misterblack1/zenith_zt1/pictures/Zenith ZT-1 Under capacitor.jpg

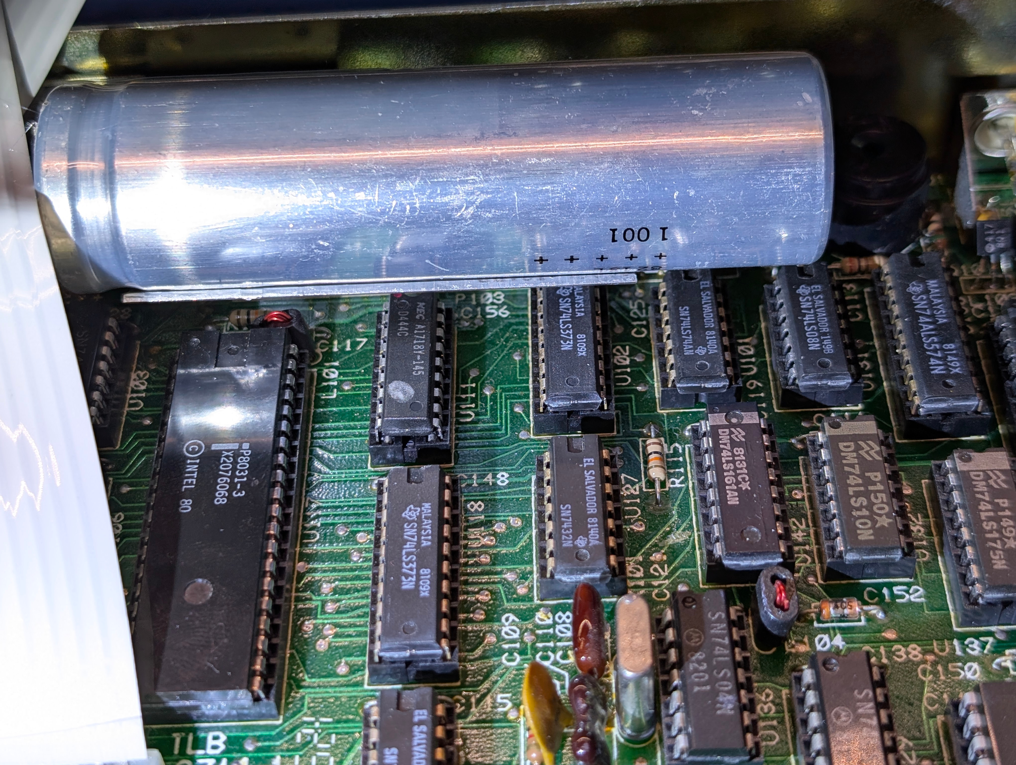
pictures/Zenith ZT-1 Under capacitor.jpg
