misterblack1/zenith_zt1/pictures/zenith_zt11/01 Zenith ZT-11.jpg

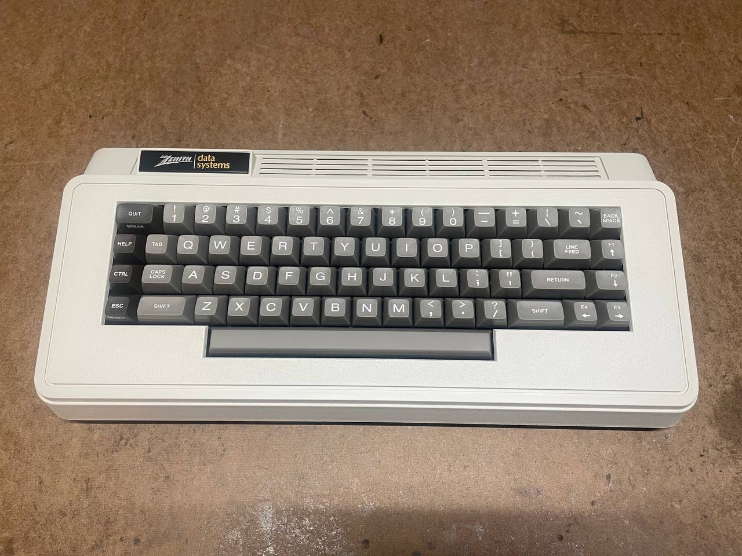
pictures/zenith_zt11/01 Zenith ZT-11.jpg
