misterblack1/zenith_zt1/pictures/zenith_zt11/02 Zenith ZT-11 Underside.jpg

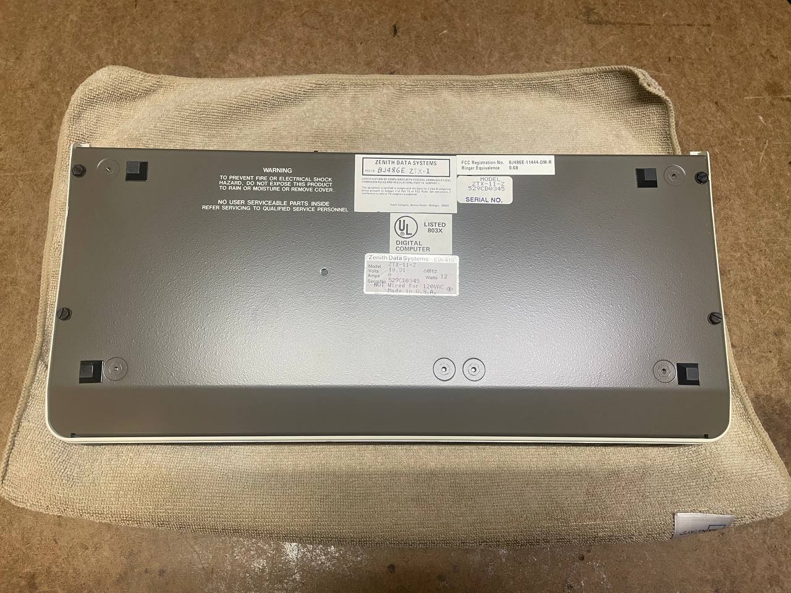
pictures/zenith_zt11/02 Zenith ZT-11 Underside.jpg
