misterblack1/zenith_zt1/pictures/zenith_zt11/03 Zenith ZT-11 Labels.jpg

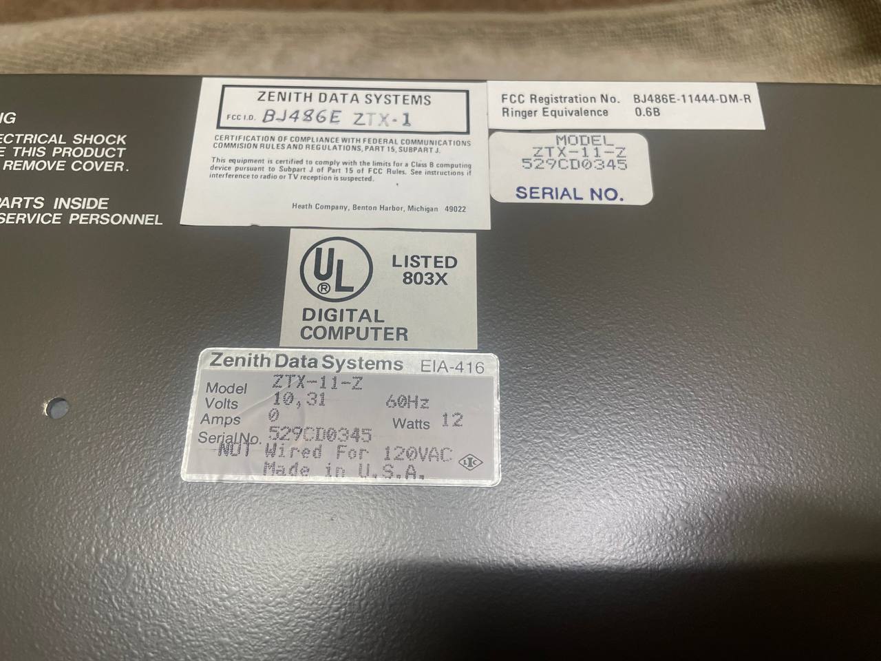
pictures/zenith_zt11/03 Zenith ZT-11 Labels.jpg
