misterblack1/zenith_zt1/pictures/zenith_zt11/04 Zenith ZT-11 Keyboard connection.jpg

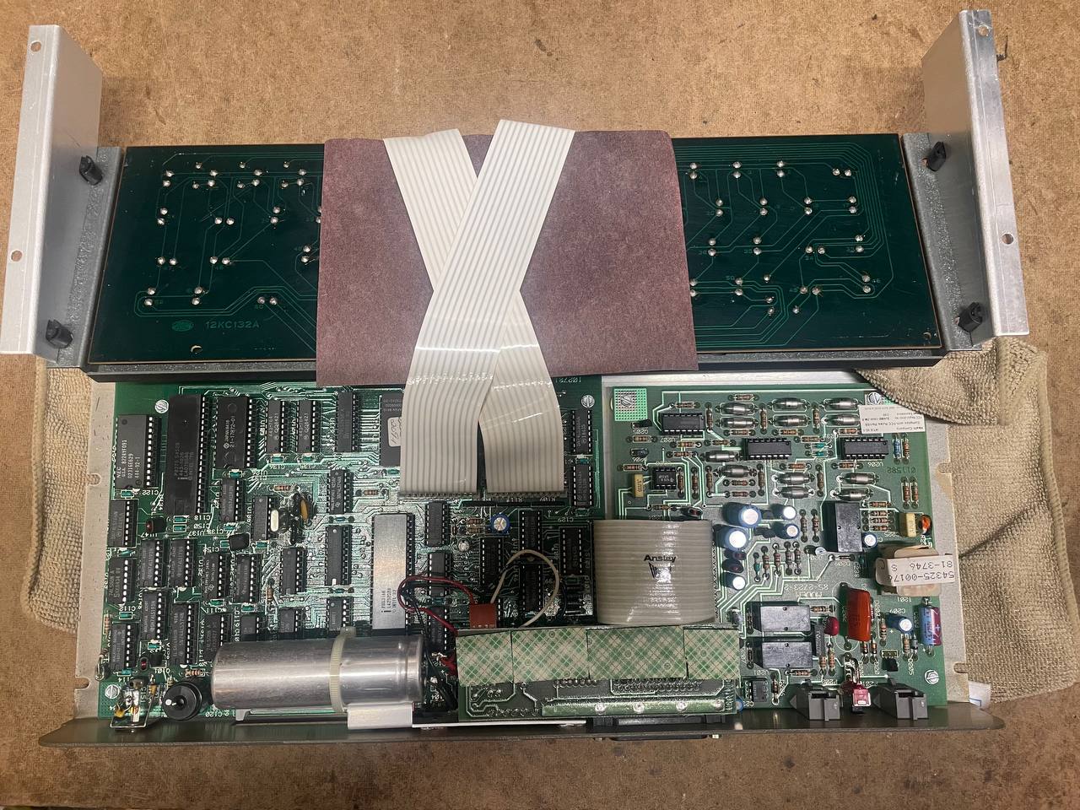
pictures/zenith_zt11/04 Zenith ZT-11 Keyboard connection.jpg
