misterblack1/zenith_zt1/pictures/zenith_zt11/05 Zenith ZT-11 Keyboard connection close up.jpg

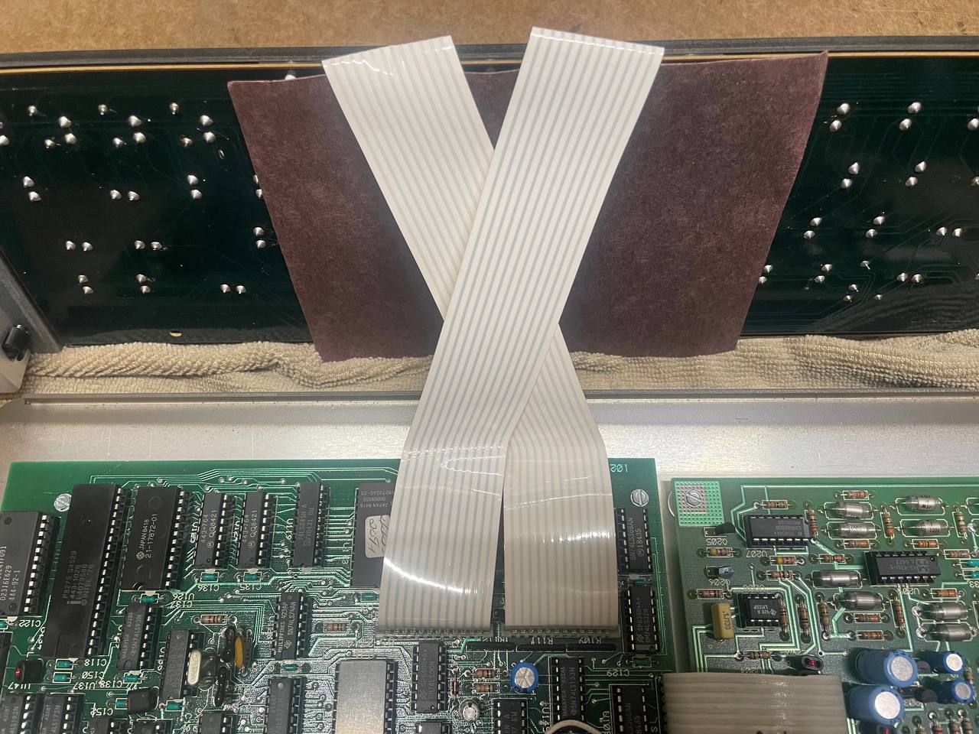
pictures/zenith_zt11/05 Zenith ZT-11 Keyboard connection close up.jpg
