misterblack1/zenith_zt1/pictures/zenith_zt11/06  Zenith ZT-11 Internals.jpg

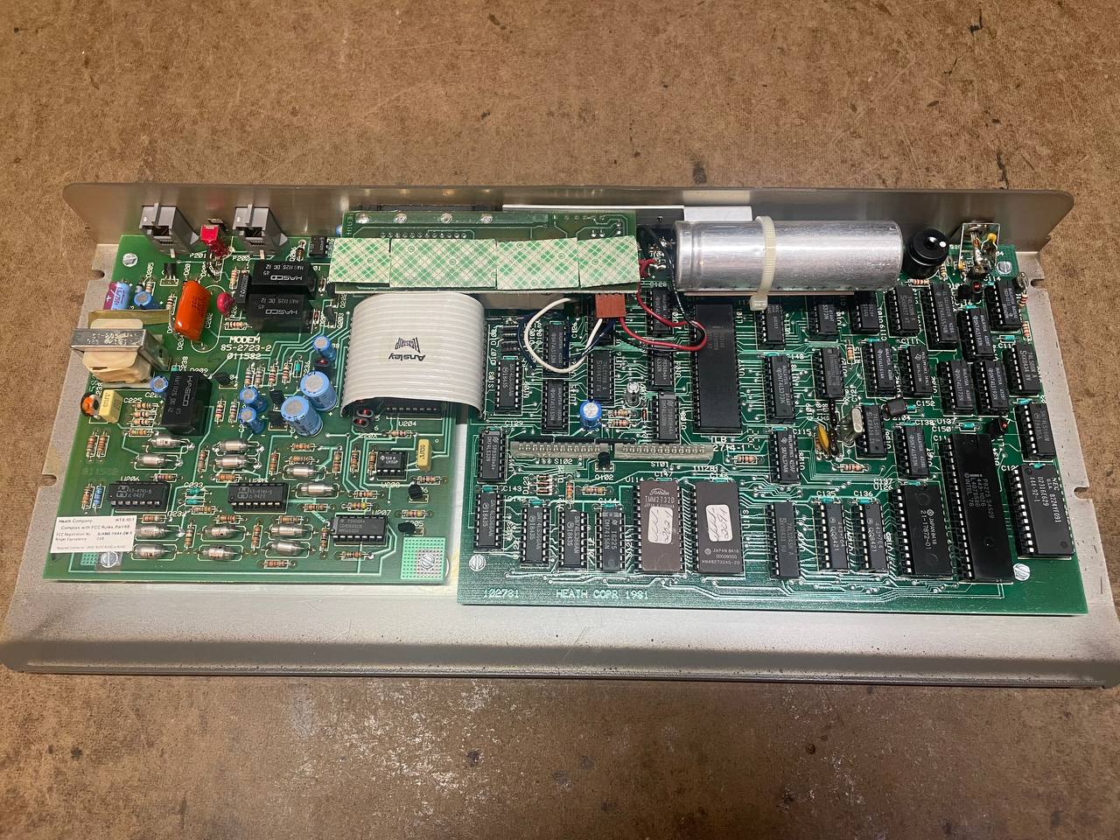
pictures/zenith_zt11/06 Zenith ZT-11 Internals.jpg
