misterblack1/zenith_zt1/pictures/zenith_zt11/08 Zenith ZT-11 Serial Add-on Board.jpg

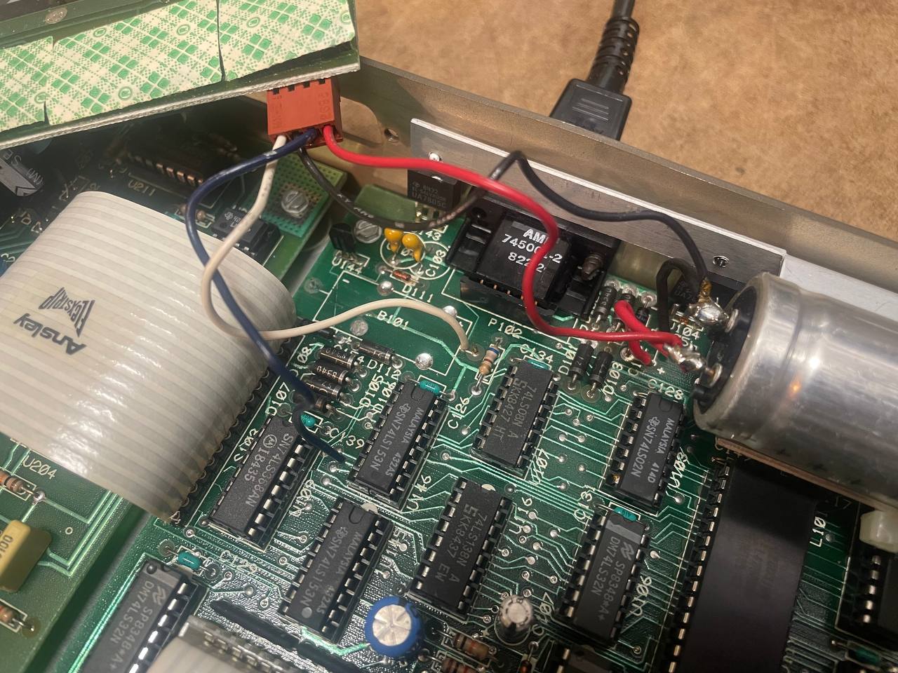
pictures/zenith_zt11/08 Zenith ZT-11 Serial Add-on Board.jpg
