misterblack1/zenith_zt1/pictures/zenith_zt11/11 Zenith ZT-11 Power on screen.jpg

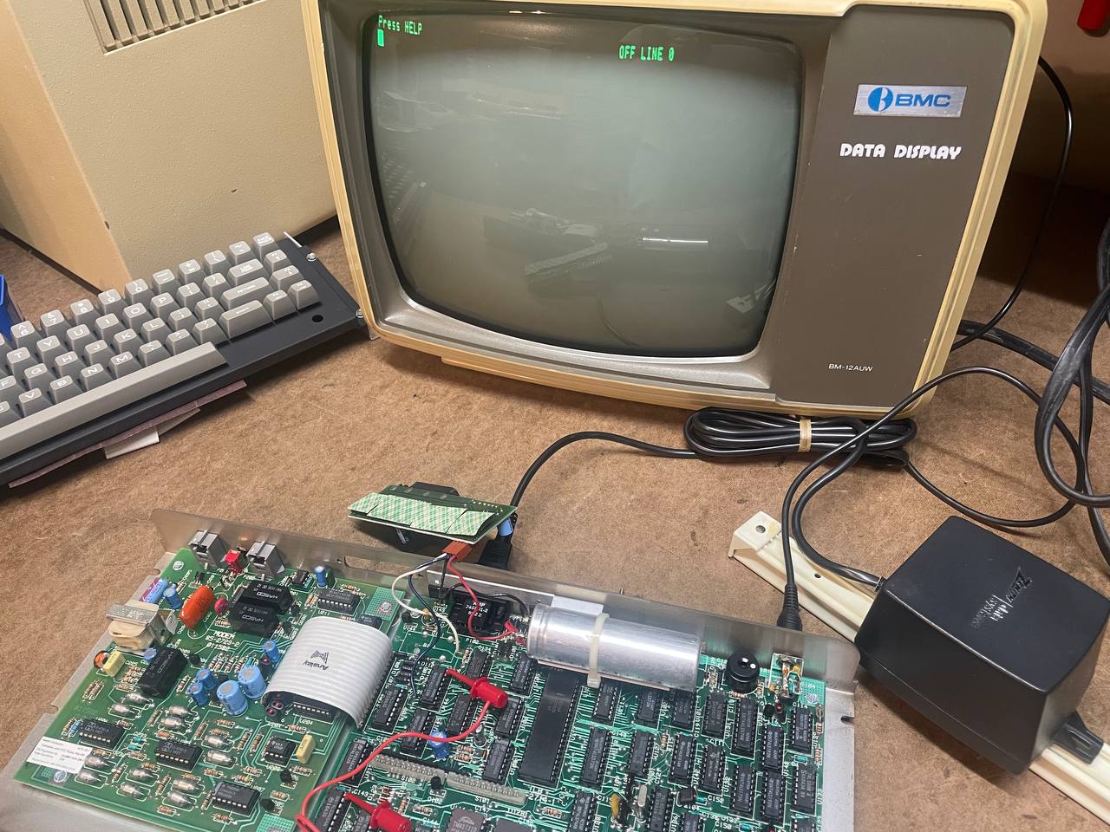
pictures/zenith_zt11/11 Zenith ZT-11 Power on screen.jpg
