misterblack1/zenith_zt1/pictures/zenith_zt11/13 Zenith ZT-11 Setup.jpg

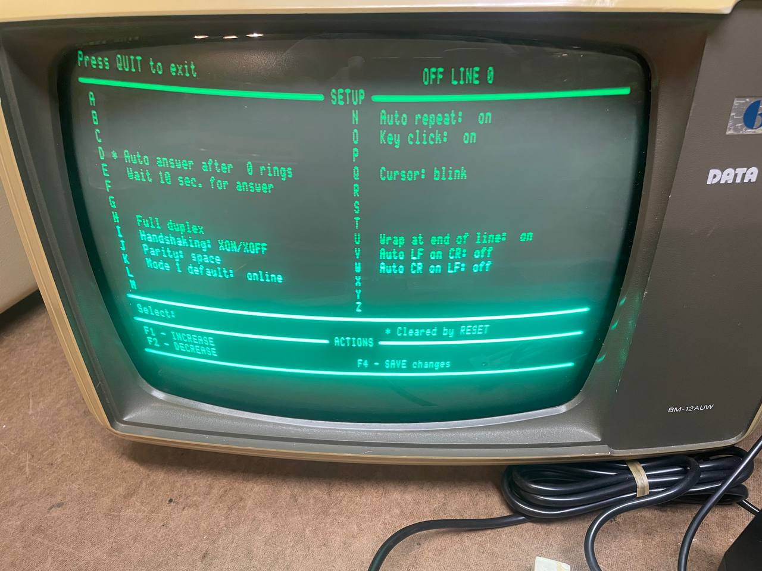
pictures/zenith_zt11/13 Zenith ZT-11 Setup.jpg
