misterblack1/zenith_zt1/ZT1 Schematics/DMA.kicad_sch

## KiCad design ZT1 Schematics/DMA.kicad_sch (2025-08-11)

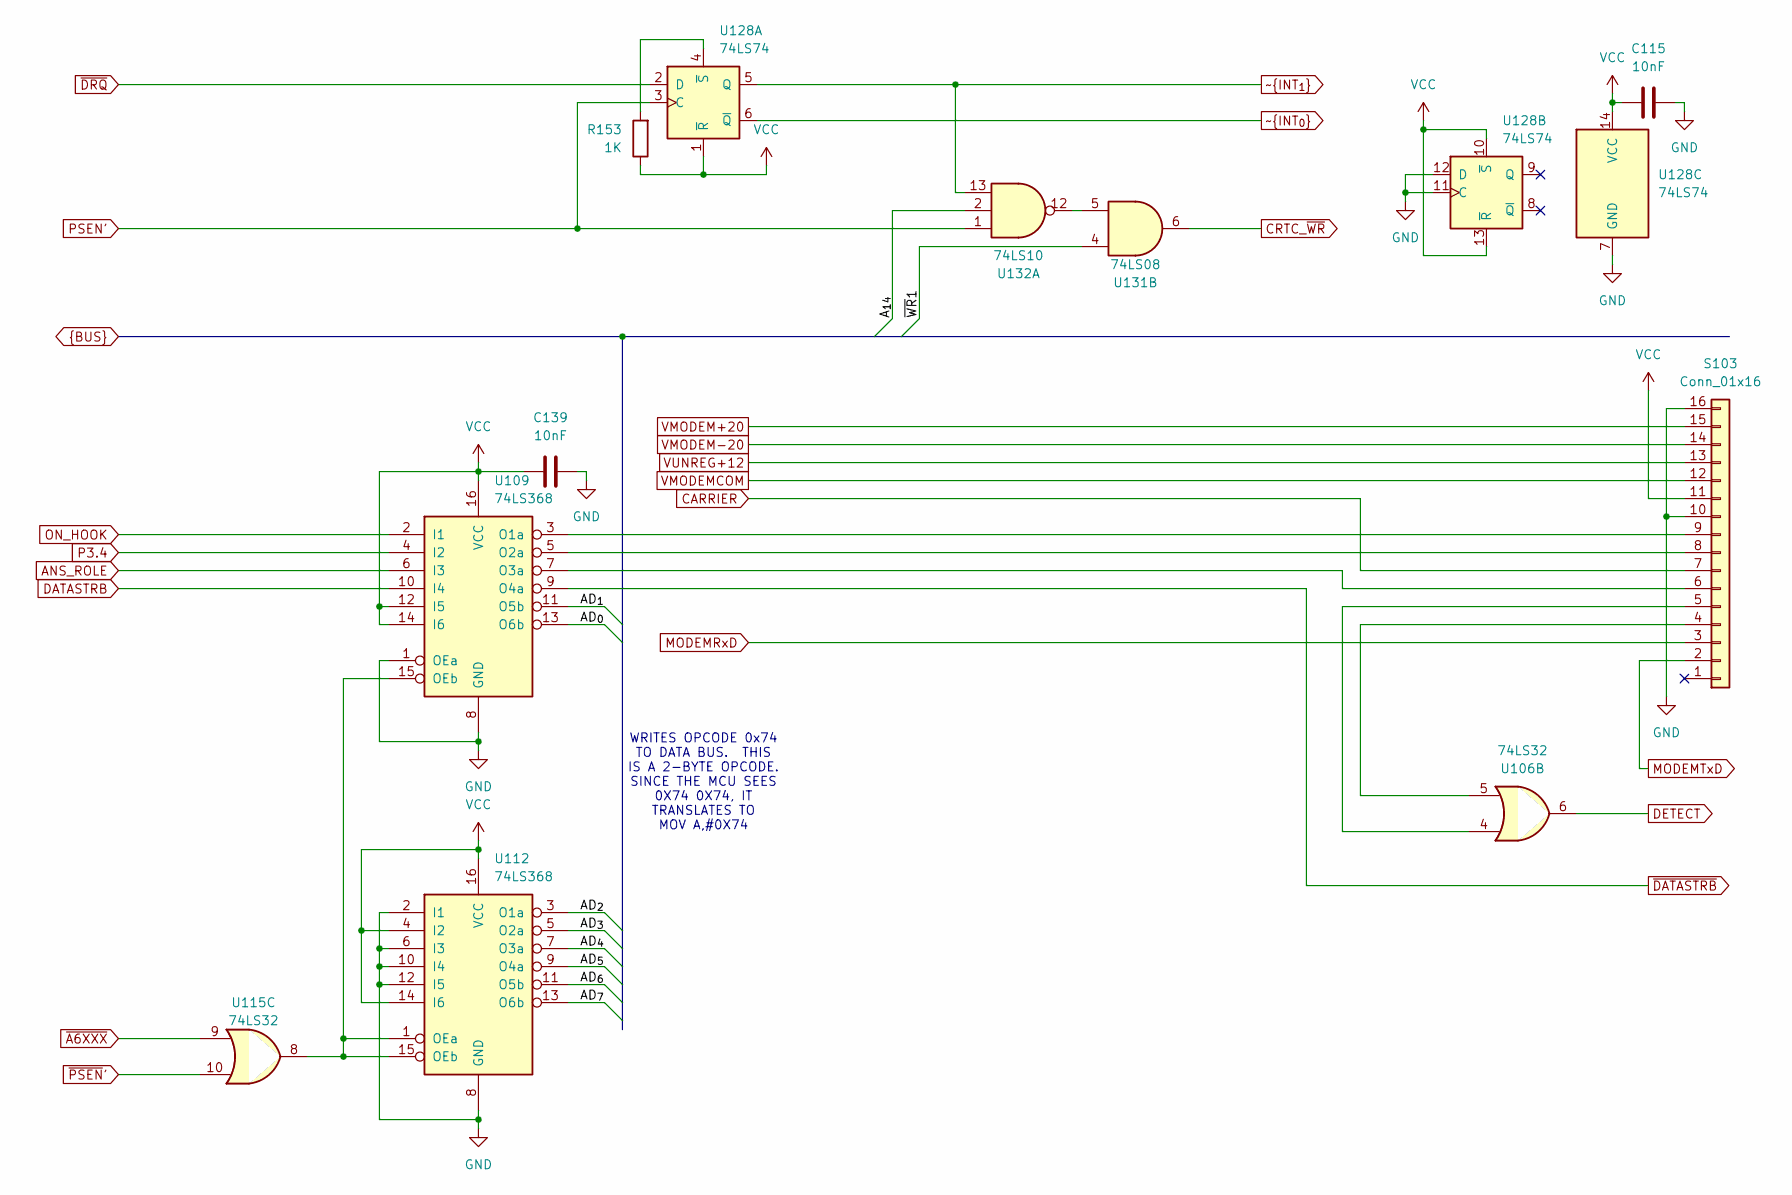
[picture p27: schematic DMA.kicad_sch]

Parts:
C115, C139: 10nF; C_350mil
R153: 1K; R_450mil
S103: Conn_01x16; PinHeader_1x16_P2.54mm_Vertical
U106, U115: 74LS32; DIP-14_W7.62mm
U109, U112: 74LS368; DIP-16_W7.62mm
U128: 74LS74; DIP-14_W7.62mm
U131: 74LS08; DIP-14_W7.62mm
U132: 74LS10; DIP-14_W7.62mm

Connections:
AD_{0}: U109.13 (O6b)
AD_{1}: U109.11 (O5b)
AD_{2}: U112.3 (O1a)
AD_{3}: U112.5 (O2a)
AD_{4}: U112.7 (O3a)
AD_{5}: U112.9 (O4a)
AD_{6}: U112.11 (O5b)
AD_{7}: U112.13 (O6b)
ANS_ROLE: U109.6 (I3)
A_{14}: U132.2
CARRIER: S103.7
CRTC_~WR: U131.6
DATASTRB: U109.10 (I4)
DETECT: U106.6
GND: C115.2, C139.2, S103.10, S103.16, U109.1 (OEa), U109.8 (GND), U112.2 (I1), U112.6 (I3), U112.8 (GND), U112.10 (I4), U112.12 (I5), U128.7 (GND), U128.11 (C), U128.12 (D)
MODEMRxD: S103.3
MODEMTxD: S103.2
unnamed: R153.2, U128.4 (~S)
unnamed: S103.4, U106.5
unnamed: S103.5, U106.4
unnamed: S103.6, U109.7 (O3a)
unnamed: S103.8, U109.5 (O2a)
unnamed: S103.9, U109.3 (O1a)
unnamed: U109.15 (OEb), U112.1 (OEa), U112.15 (OEb), U115.8
unnamed: U131.5, U132.12
ON_HOOK: U109.2 (I1)
P3.4: U109.4 (I2)
PSEN': U128.3 (C), U132.1
VCC: C115.1, C139.1, R153.1, S103.11, U109.12 (I5), U109.14 (I6), U109.16 (VCC), U112.4 (I2), U112.14 (I6), U112.16 (VCC), U128.1 (~R), U128.10 (~S), U128.13 (~R), U128.14 (VCC)
VMODEM+20: S103.15
VMODEM-20: S103.14
VMODEMCOM: S103.12
VUNREG+12: S103.13
~A6XXX: U115.9
~DATASTRB: U109.9 (O4a)
~DRQ: U128.2 (D)
~INT_{0}: U128.6 (~Q)
~INT_{1}: U128.5 (Q), U132.13
~PSEN': U115.10
~WR1: U131.4

Notes on the sheet:
WRITES OPCODE 0x74 TO DATA BUS. THIS IS A 2-BYTE OPCODE. SINCE THE MCU SEES 0X74 0X74, IT TRANSLATES TO MOV A,#0X74
