misterblack1/zenith_zt1/ZT1 Schematics/MCU.kicad_sch

## KiCad design ZT1 Schematics/MCU.kicad_sch (2025-08-11)

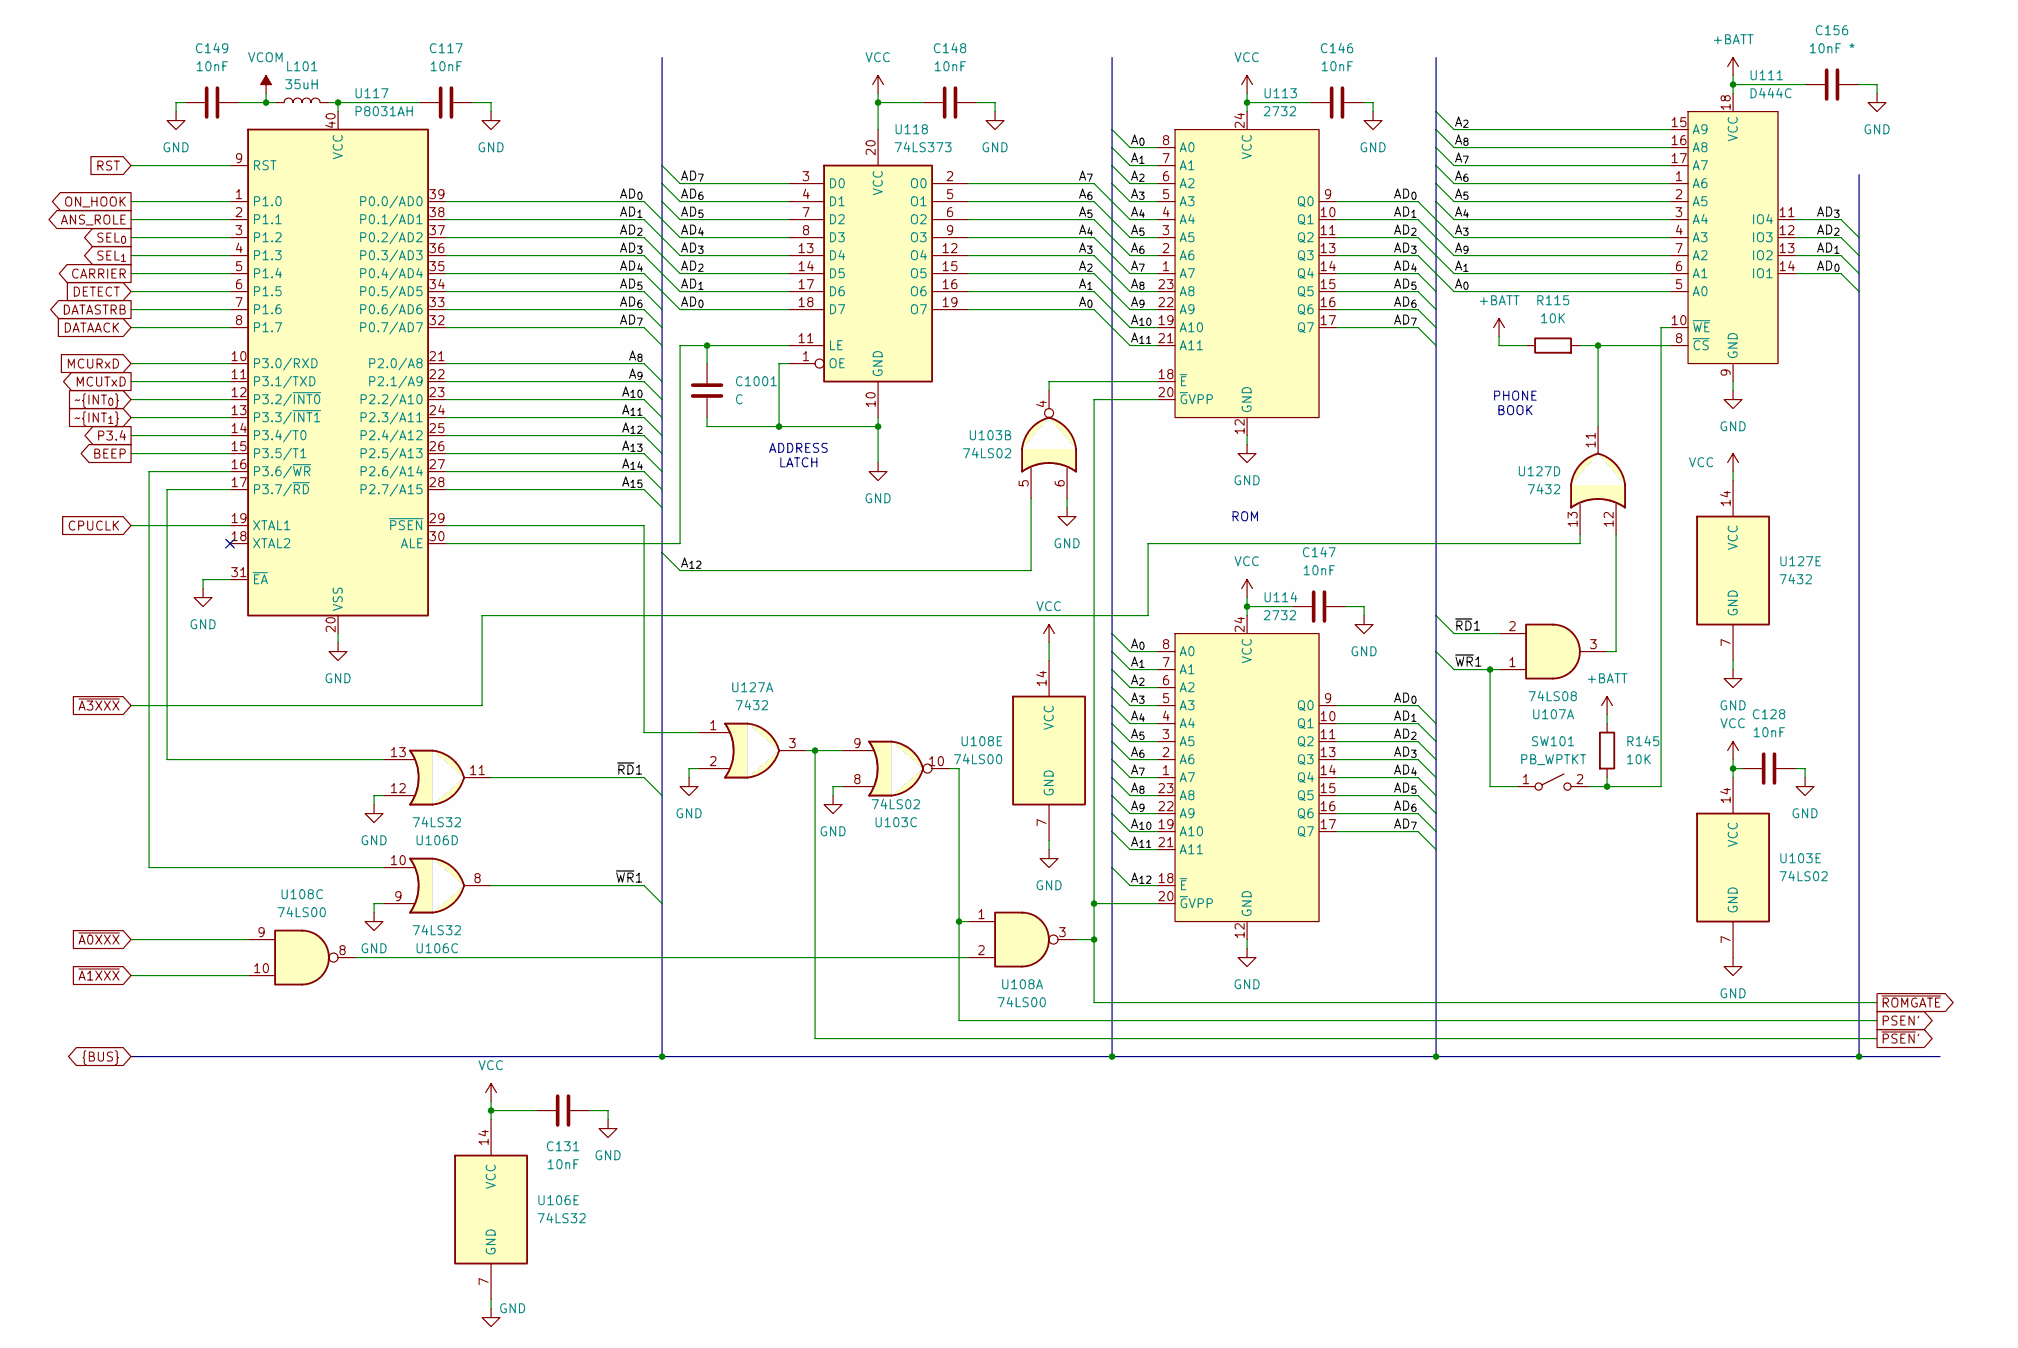
[picture p28: schematic MCU.kicad_sch]

Parts:
C117, C128, C131, C146, C147, C148, C149: 10nF; C_350mil
C156: 10nF *; C_350mil
C1001: C; C_Disc_P7.62
L101: 35uH; L_Axial_L7.0mm_D3.3mm_P5.08mm_Vertical_Fastron_MICC
R115, R145: 10K; R_450mil
SW101: PB_WPTKT; SW_DIP_SPSTx01_Slide_6.7x4.1mm_W7.62mm_P2.54mm_LowProfile
U103: 74LS02; DIP-14_W7.62mm
U106: 74LS32; DIP-14_W7.62mm
U107: 74LS08; DIP-14_W7.62mm
U108: 74LS00; DIP-14_W7.62mm
U111: D444C; DIP-18_W7.62mm
U113, U114: 2732; DIP-24_W15.24mm
U117: P8031AH; DIP-40_W15.24mm
U118: 74LS373; DIP-20_W7.62mm
U127: 7432; DIP-14_W7.62mm

Connections:
+BATT: C156.1, R115.1, R145.1, U111.18 (VCC)
AD_{0}: U111.14 (IO1), U113.9 (Q0), U114.9 (Q0), U117.39 (P0.0/AD0), U118.18 (D7)
AD_{1}: U111.13 (IO2), U113.10 (Q1), U114.10 (Q1), U117.38 (P0.1/AD1), U118.17 (D6)
AD_{2}: U111.12 (IO3), U113.11 (Q2), U114.11 (Q2), U117.37 (P0.2/AD2), U118.14 (D5)
AD_{3}: U111.11 (IO4), U113.13 (Q3), U114.13 (Q3), U117.36 (P0.3/AD3), U118.13 (D4)
AD_{4}: U113.14 (Q4), U114.14 (Q4), U117.35 (P0.4/AD4), U118.8 (D3)
AD_{5}: U113.15 (Q5), U114.15 (Q5), U117.34 (P0.5/AD5), U118.7 (D2)
AD_{6}: U113.16 (Q6), U114.16 (Q6), U117.33 (P0.6/AD6), U118.4 (D1)
AD_{7}: U113.17 (Q7), U114.17 (Q7), U117.32 (P0.7/AD7), U118.3 (D0)
ANS_ROLE: U117.2 (P1.1)
A_{0}: U111.5 (A0), U113.8 (A0), U114.8 (A0), U118.19 (O7)
A_{1}: U111.6 (A1), U113.7 (A1), U114.7 (A1), U118.16 (O6)
A_{2}: U111.15 (A9), U113.6 (A2), U114.6 (A2), U118.15 (O5)
A_{3}: U111.4 (A3), U113.5 (A3), U114.5 (A3), U118.12 (O4)
A_{4}: U111.3 (A4), U113.4 (A4), U114.4 (A4), U118.9 (O3)
A_{5}: U111.2 (A5), U113.3 (A5), U114.3 (A5), U118.6 (O2)
A_{6}: U111.1 (A6), U113.2 (A6), U114.2 (A6), U118.5 (O1)
A_{7}: U111.17 (A7), U113.1 (A7), U114.1 (A7), U118.2 (O0)
A_{8}: U111.16 (A8), U113.23 (A8), U114.23 (A8), U117.21 (P2.0/A8)
A_{9}: U111.7 (A2), U113.22 (A9), U114.22 (A9), U117.22 (P2.1/A9)
A_{10}: U113.19 (A10), U114.19 (A10), U117.23 (P2.2/A10)
A_{11}: U113.21 (A11), U114.21 (A11), U117.24 (P2.3/A11)
A_{12}: U103.5, U114.18 (~E), U117.25 (P2.4/A12)
A_{13}: U117.26 (P2.5/A13)
A_{14}: U117.27 (P2.6/A14)
A_{15}: U117.28 (P2.7/A15)
BEEP: U117.15 (P3.5/T1)
CARRIER: U117.5 (P1.4)
CPUCLK: U117.19 (XTAL1)
DATAACK: U117.8 (P1.7)
DATASTRB: U117.7 (P1.6)
DETECT: U117.6 (P1.5)
GND: C117.2, C128.2, C131.2, C146.2, C147.2, C148.2, C149.1, C156.2, C1001.2, U103.6, U103.7 (GND), U103.8, U106.7 (GND), U106.9, U106.12, U108.7 (GND), U111.9 (GND), U113.12 (GND), U114.12 (GND), U117.20 (VSS), U117.31 (~EA), U118.1 (OE), U118.10 (GND), U127.2, U127.7 (GND)
MCURxD: U117.10 (P3.0/RXD)
MCUTxD: U117.11 (P3.1/TXD)
unnamed: C117.1, L101.2, U117.40 (VCC)
unnamed: C1001.1, U117.30 (ALE), U118.11 (LE)
unnamed: R115.2, U111.8 (~CS), U127.11
unnamed: R145.2, SW101.2 (B), U111.10 (~WE)
unnamed: U103.4, U113.18 (~E)
unnamed: U106.10, U117.16 (P3.6/~WR)
unnamed: U106.13, U117.17 (P3.7/~RD)
unnamed: U107.3, U127.12
unnamed: U108.2, U108.8
unnamed: U117.29 (~PSEN), U127.1
ON_HOOK: U117.1 (P1.0)
P3.4: U117.14 (P3.4/T0)
PSEN': U103.10, U108.1
RST: U117.9 (RST)
SEL_{0}: U117.3 (P1.2)
SEL_{1}: U117.4 (P1.3)
VCC: C128.1, C131.1, C146.1, C147.1, C148.1, U103.14 (VCC), U106.14 (VCC), U108.14 (VCC), U113.24 (VCC), U114.24 (VCC), U118.20 (VCC), U127.14 (VCC)
VCOM: C149.2, L101.1
~A0XXX: U108.9
~A1XXX: U108.10
~A3XXX: U127.13
~INT_{0}: U117.12 (P3.2/~INT0)
~INT_{1}: U117.13 (P3.3/~INT1)
~PSEN': U103.9, U127.3
~RD1: U106.11, U107.2
~ROMGATE: U108.3, U113.20 (~GVPP), U114.20 (~GVPP)
~WR1: SW101.1 (A), U106.8, U107.1

Notes on the sheet:
PHONE BOOK
ROM
ADDRESS LATCH
