misterblack1/zenith_zt1/ZT1 Schematics/Oscillator.kicad_sch

## KiCad design ZT1 Schematics/Oscillator.kicad_sch (2025-08-11)

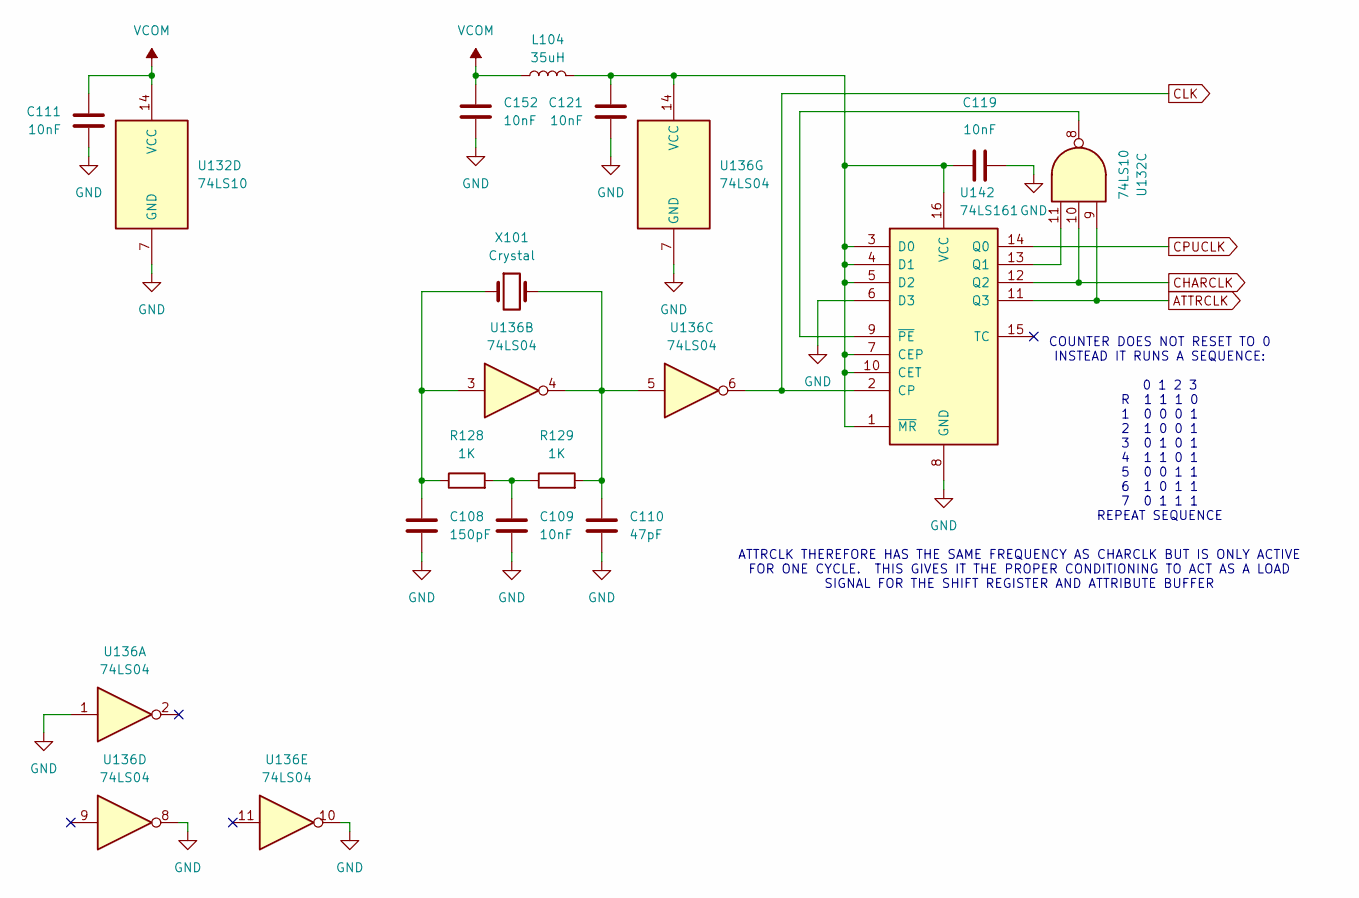
[picture p29: schematic Oscillator.kicad_sch]

Parts:
C108: 150pF; C_Disc_D9.0mm_W2.5mm_P7.50mm
C109: 10nF; C_Disc_D9.0mm_W2.5mm_P7.50mm
C110: 47pF; C_Disc_D9.0mm_W2.5mm_P7.50mm
C111, C119, C121, C152: 10nF; C_350mil
L104: 35uH; L_Axial_L7.0mm_D3.3mm_P5.08mm_Vertical_Fastron_MICC
R128, R129: 1K; R_450mil
U132: 74LS10; DIP-14_W7.62mm
U136: 74LS04; DIP-14_W7.62mm
U142: 74LS161; DIP-16_W7.62mm
X101: Crystal; Crystal_HC18-U_Vertical

Connections:
ATTRCLK: U132.9, U142.11 (Q3)
CHARCLK: U132.10, U142.12 (Q2)
CLK: U136.6, U142.2 (CP)
CPUCLK: U142.14 (Q0)
GND: C108.2, C109.2, C110.2, C111.2, C119.2, C121.2, C152.2, U132.7 (GND), U136.1, U136.7 (GND), U136.8, U136.10, U142.6 (D3), U142.8 (GND)
unnamed: C108.1, R128.1, U136.3, X101.1
unnamed: C109.1, R128.2, R129.1
unnamed: C110.1, R129.2, U136.4, U136.5, X101.2
unnamed: C119.1, C121.1, L104.2, U136.14 (VCC), U142.1 (~MR), U142.3 (D0), U142.4 (D1), U142.5 (D2), U142.7 (CEP), U142.10 (CET), U142.16 (VCC)
unnamed: U132.8, U142.9 (~PE)
unnamed: U132.11, U142.13 (Q1)
VCOM: C111.1, C152.1, L104.1, U132.14 (VCC)

Notes on the sheet:
ATTRCLK THEREFORE HAS THE SAME FREQUENCY AS CHARCLK BUT IS ONLY ACTIVE FOR ONE CYCLE. THIS GIVES IT THE PROPER CONDITIONING TO ACT AS A LOAD SIGNAL FOR THE SHIFT REGISTER AND ATTRIBUTE BUFFER
COUNTER DOES NOT RESET TO 0 INSTEAD IT RUNS A SEQUENCE: 0 1 2 3 R 1 1 1 0 1 0 0 0 1 2 1 0 0 1 3 0 1 0 1 4 1 1 0 1 5 0 0 1 1 6 1 0 1 1 7 0 1 1 1 REPEAT SEQUENCE
