misterblack1/zenith_zt1/ZT1 Schematics/VRAM.kicad_sch

## KiCad design ZT1 Schematics/VRAM.kicad_sch (2025-08-11)

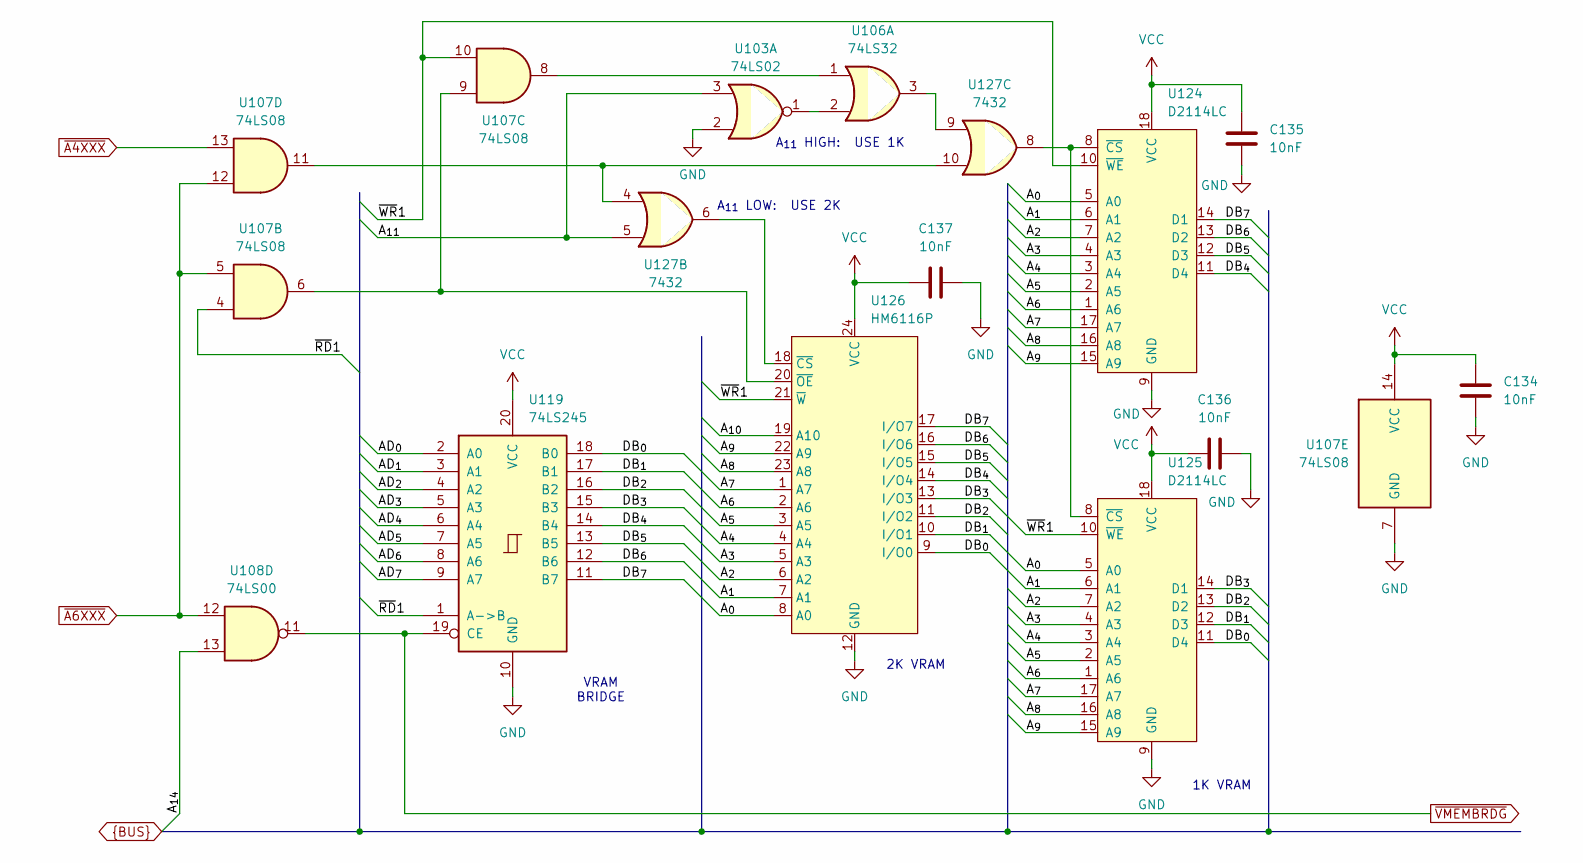
[picture p30: schematic VRAM.kicad_sch]

Parts:
C134, C135, C136, C137: 10nF; C_350mil
U103: 74LS02; DIP-14_W7.62mm
U106: 74LS32; DIP-14_W7.62mm
U107: 74LS08; DIP-14_W7.62mm
U108: 74LS00; DIP-14_W7.62mm
U119: 74LS245; DIP-20_W7.62mm
U124, U125: D2114LC; DIP-18_W7.62mm
U126: HM6116P; DIP-24_W15.24mm
U127: 7432; DIP-14_W7.62mm

Connections:
AD_{0}: U119.2 (A0)
AD_{1}: U119.3 (A1)
AD_{2}: U119.4 (A2)
AD_{3}: U119.5 (A3)
AD_{4}: U119.6 (A4)
AD_{5}: U119.7 (A5)
AD_{6}: U119.8 (A6)
AD_{7}: U119.9 (A7)
A_{0}: U124.5 (A0), U125.5 (A0), U126.8 (A0)
A_{1}: U124.6 (A1), U125.6 (A1), U126.7 (A1)
A_{2}: U124.7 (A2), U125.7 (A2), U126.6 (A2)
A_{3}: U124.4 (A3), U125.4 (A3), U126.5 (A3)
A_{4}: U124.3 (A4), U125.3 (A4), U126.4 (A4)
A_{5}: U124.2 (A5), U125.2 (A5), U126.3 (A5)
A_{6}: U124.1 (A6), U125.1 (A6), U126.2 (A6)
A_{7}: U124.17 (A7), U125.17 (A7), U126.1 (A7)
A_{8}: U124.16 (A8), U125.16 (A8), U126.23 (A8)
A_{9}: U124.15 (A9), U125.15 (A9), U126.22 (A9)
A_{10}: U126.19 (A10)
A_{11}: U103.3, U127.5
A_{14}: U108.13
DB_{0}: U119.18 (B0), U125.11 (D4), U126.9 (I/O0)
DB_{1}: U119.17 (B1), U125.12 (D3), U126.10 (I/O1)
DB_{2}: U119.16 (B2), U125.13 (D2), U126.11 (I/O2)
DB_{3}: U119.15 (B3), U125.14 (D1), U126.13 (I/O3)
DB_{4}: U119.14 (B4), U124.11 (D4), U126.14 (I/O4)
DB_{5}: U119.13 (B5), U124.12 (D3), U126.15 (I/O5)
DB_{6}: U119.12 (B6), U124.13 (D2), U126.16 (I/O6)
DB_{7}: U119.11 (B7), U124.14 (D1), U126.17 (I/O7)
GND: C134.2, C135.2, C136.2, C137.2, U103.2, U107.7 (GND), U119.10 (GND), U124.9 (GND), U125.9 (GND), U126.12 (GND)
unnamed: U103.1, U106.2
unnamed: U106.1, U107.8
unnamed: U106.3, U127.9
unnamed: U107.6, U107.9, U126.20 (~OE)
unnamed: U107.11, U127.4, U127.10
unnamed: U124.8 (~CS), U125.8 (~CS), U127.8
unnamed: U126.18 (~CS), U127.6
VCC: C134.1, C135.1, C136.1, C137.1, U107.14 (VCC), U119.20 (VCC), U124.18 (VCC), U125.18 (VCC), U126.24 (VCC)
~A4XXX: U107.13
~A6XXX: U107.5, U107.12, U108.12
~RD1: U107.4, U119.1 (A->B)
~VMEMBRDG: U108.11, U119.19 (CE)
~WR1: U107.10, U124.10 (~WE), U125.10 (~WE), U126.21 (~W)

Notes on the sheet:
2K VRAM
VRAM BRIDGE
A_{11} HIGH: USE 1K
1K VRAM
A_{11} LOW: USE 2K
