misterblack1/zenith_zt1/ZT1 Schematics/ZX1.kicad_sch

## KiCad design ZT1 Schematics/ZX1.kicad_sch (2025-08-11)

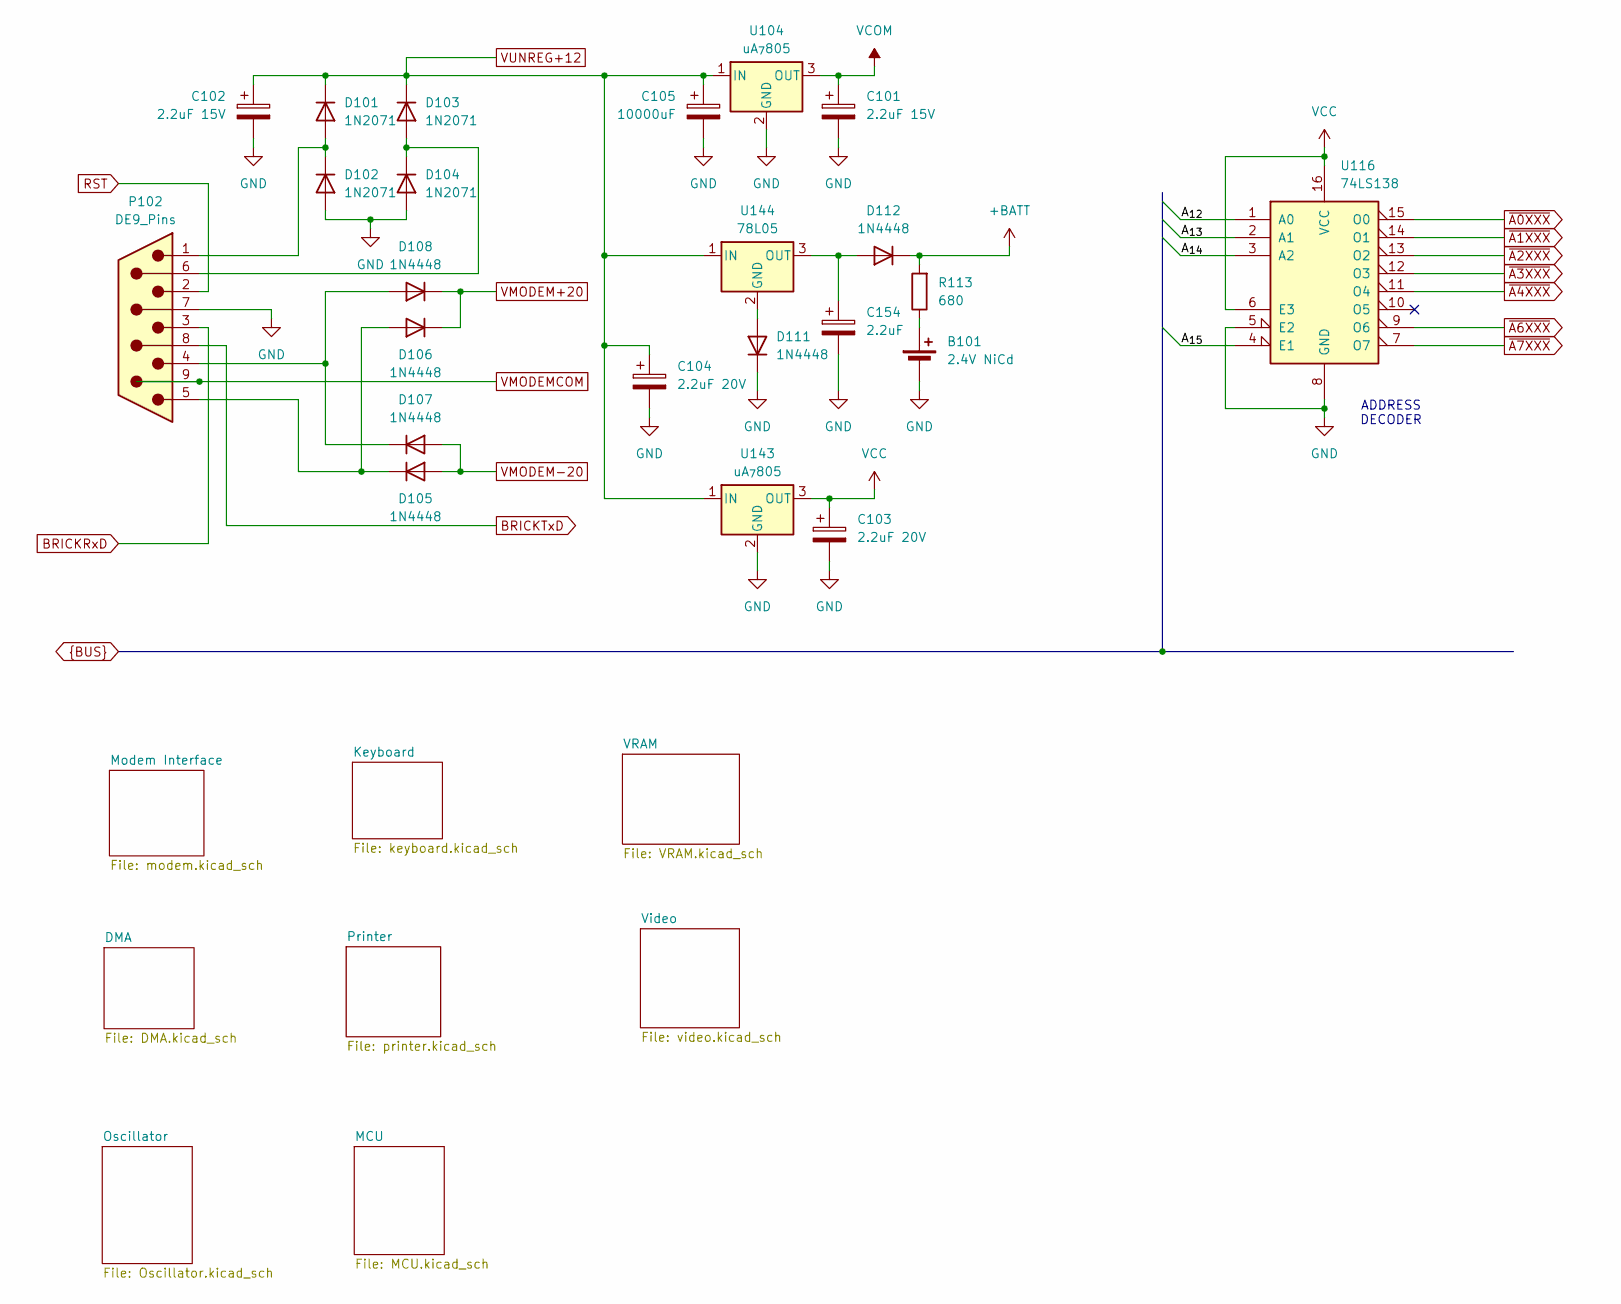
[picture p31: schematic ZX1.kicad_sch]

Parts:
B101: 2.4V NiCd; Battery
C101, C102: 2.2uF 15V; CP_520mil
C103, C104: 2.2uF 20V; CP_Radial_D8.0mm_P5.00mm
C105: 10000uF; CP_Radial_D10.0mm_P5.00mm
C154: 2.2uF; CP_350mil
D101, D102, D103, D104: 1N2071; D_DO-34_SOD68_P10.16mm_Horizontal
D105, D106, D107, D108, D111, D112: 1N4448; D_350mil
P102: DE9_Pins; DSUB-9_Pins_Horizontal_P2.77x2.54mm_EdgePinOffset9.40mm
R113: 680; R_450mil
U104, U143: uA_{7}805; TO-220-3_Vertical
U116: 74LS138; DIP-16_W7.62mm
U144: 78L05; TO-220-3_Vertical

Connections:
+BATT: D112.1 (K), R113.2
A_{12}: U116.1 (A0)
A_{13}: U116.2 (A1)
A_{14}: U116.3 (A2)
A_{15}: U116.4 (E1)
BRICKRxD: P102.3
BRICKTxD: P102.8
GND: B101.2 (-), C101.2, C102.2, C103.2, C104.2, C105.2, C154.2, D102.2 (A), D104.2 (A), D111.1 (K), P102.7, U104.2 (GND), U116.5 (E2), U116.8 (GND), U143.2 (GND)
unnamed: B101.1 (+), R113.1
unnamed: C154.1, D112.2 (A), U144.3 (OUT)
unnamed: D101.2 (A), D102.1 (K), P102.1
unnamed: D103.2 (A), D104.1 (K), P102.6
unnamed: D105.1 (K), D106.2 (A), P102.5
unnamed: D107.1 (K), D108.2 (A), P102.4
unnamed: D111.2 (A), U144.2 (GND)
RST: P102.2
VCC: C103.1, U116.6 (E3), U116.16 (VCC), U143.3 (OUT)
VCOM: C101.1, U104.3 (OUT)
VMODEM+20: D106.1 (K), D108.1 (K)
VMODEM-20: D105.2 (A), D107.2 (A)
VMODEMCOM: P102.9
VUNREG+12: C102.1, C104.1, C105.1, D101.1 (K), D103.1 (K), U104.1 (IN), U143.1 (IN), U144.1 (IN)
~A0XXX: U116.15 (O0)
~A1XXX: U116.14 (O1)
~A2XXX: U116.13 (O2)
~A3XXX: U116.12 (O3)
~A4XXX: U116.11 (O4)
~A6XXX: U116.9 (O6)
~A7XXX: U116.7 (O7)

Notes on the sheet:
ADDRESS DECODER
