misterblack1/zenith_zt1/ZT1 Schematics/keyboard.kicad_sch

## KiCad design ZT1 Schematics/keyboard.kicad_sch (2025-08-11)

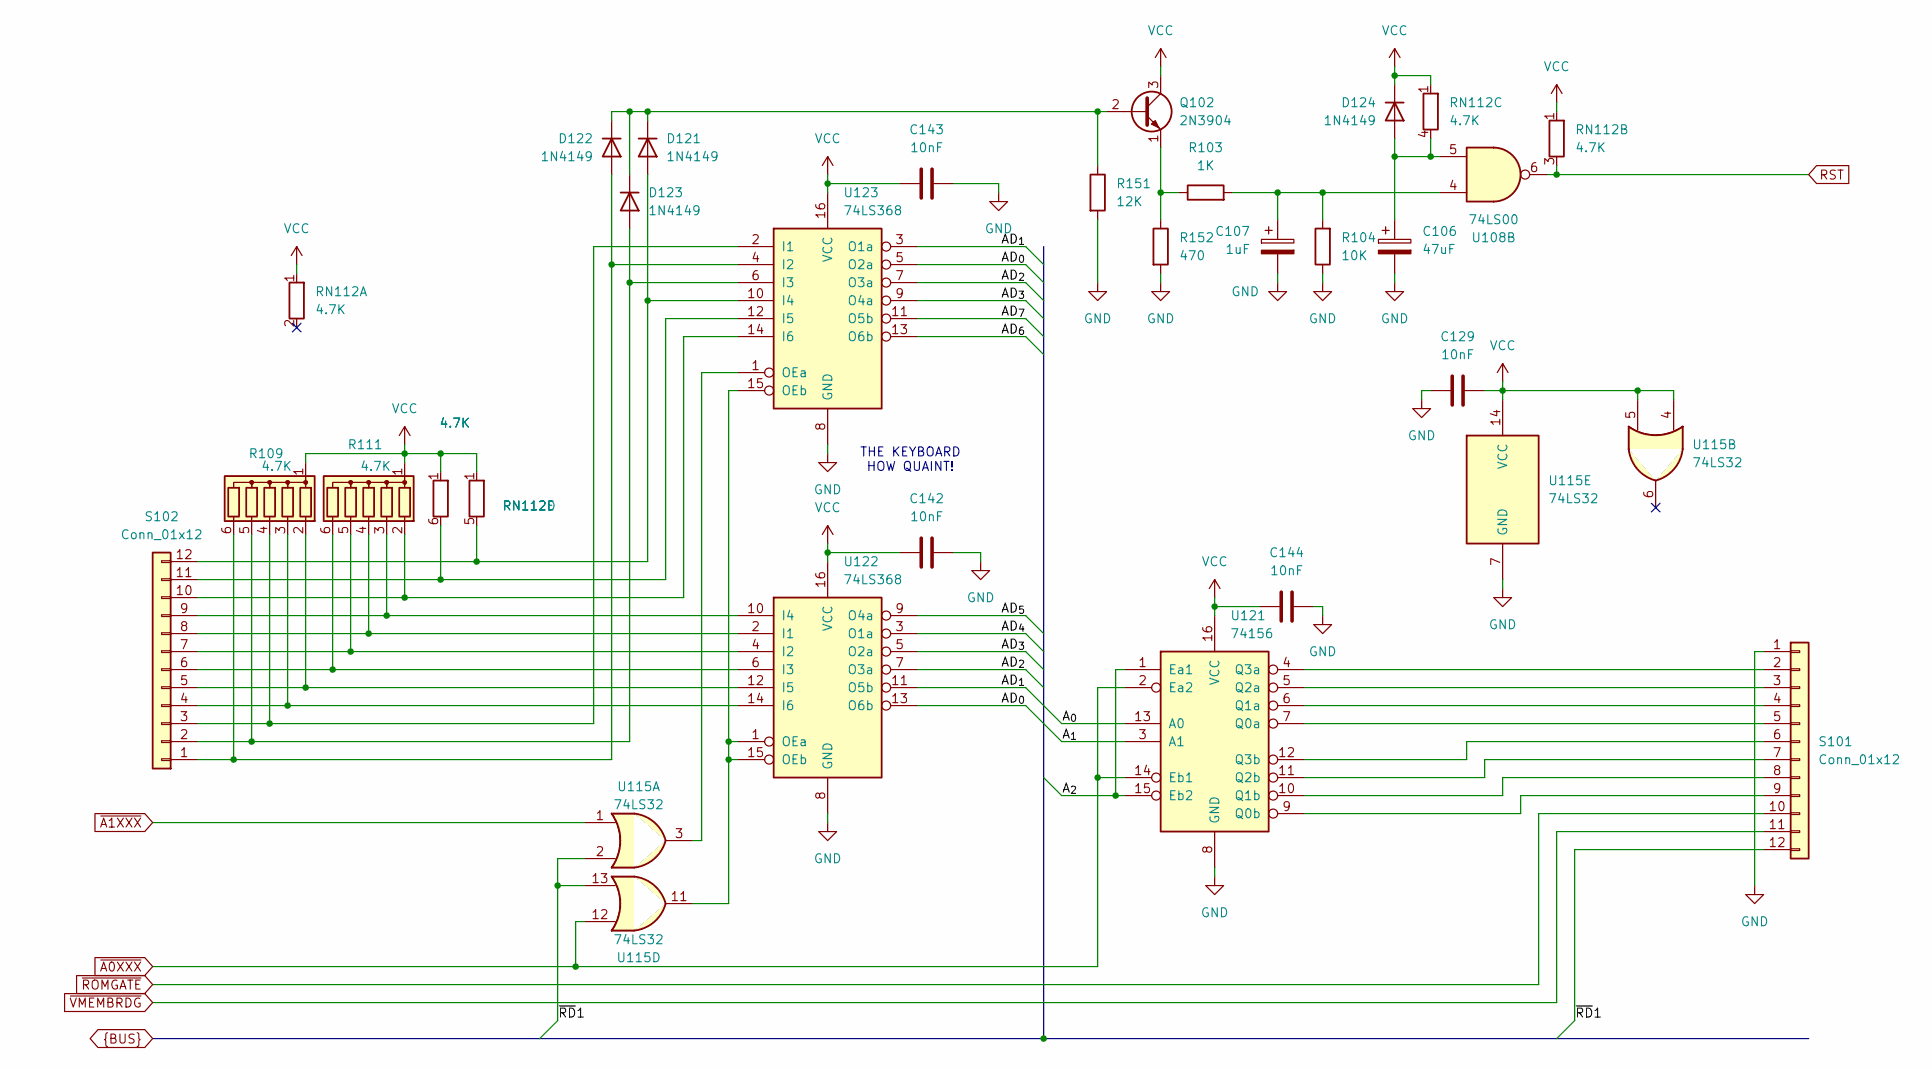
[picture p32: schematic keyboard.kicad_sch]

Parts:
C106: 47uF; CP_Radial_D5.0mm_P2.50mm
C107: 1uF; CP_Radial_D5.0mm_P2.50mm
C129, C142, C143, C144: 10nF; C_350mil
D121, D122, D123, D124: 1N4149; D_350mil
Q102: 2N3904; TO-92L_Inline_Wide
R103: 1K; R_450mil
R104: 10K; R_450mil
R109, R111: 4.7K; R_Array_SIP6
R151: 12K; R_450mil
R152: 470; R_450mil
RN112: 4.7K; R_Array_SIP6
S101, S102: Conn_01x12; PinHeader_1x12_P2.54mm_Vertical
U108: 74LS00; DIP-14_W7.62mm
U115: 74LS32; DIP-14_W7.62mm
U121: 74156; DIP-16_W7.62mm
U122, U123: 74LS368; DIP-16_W7.62mm

Connections:
AD_{0}: U122.13 (O6b), U123.5 (O2a)
AD_{1}: U122.11 (O5b), U123.3 (O1a)
AD_{2}: U122.7 (O3a), U123.7 (O3a)
AD_{3}: U122.5 (O2a), U123.9 (O4a)
AD_{4}: U122.3 (O1a)
AD_{5}: U122.9 (O4a)
AD_{6}: U123.13 (O6b)
AD_{7}: U123.11 (O5b)
A_{0}: U121.13 (A0)
A_{1}: U121.3 (A1)
A_{2}: U121.1 (Ea1), U121.15 (Eb2)
GND: C106.2, C107.2, C129.1, C142.1, C143.2, C144.2, R104.1, R151.2, R152.2, S101.1, U115.7 (GND), U121.8 (GND), U122.8 (GND), U123.8 (GND)
unnamed: C106.1, D124.2 (A), RN112.4 (R3.2), U108.5
unnamed: C107.1, R103.2, R104.2, U108.4
unnamed: D121.1 (K), D122.1 (K), D123.1 (K), Q102.2 (B), R151.1
unnamed: D121.2 (A), RN112.5 (R4.2), S102.12, U123.10 (I4)
unnamed: D122.2 (A), R109.6 (R5), S102.1, U123.4 (I2)
unnamed: D123.2 (A), R109.5 (R4), S102.2, U123.6 (I3)
unnamed: Q102.1 (E), R103.1, R152.1
unnamed: R109.2 (R1), S102.5, U122.12 (I5)
unnamed: R109.3 (R2), S102.4, U122.14 (I6)
unnamed: R109.4 (R3), S102.3, U123.2 (I1)
unnamed: R111.2 (R1), S102.10, U123.14 (I6)
unnamed: R111.3 (R2), S102.9, U122.10 (I4)
unnamed: R111.4 (R3), S102.8, U122.2 (I1)
unnamed: R111.5 (R4), S102.7, U122.4 (I2)
unnamed: R111.6 (R5), S102.6, U122.6 (I3)
unnamed: RN112.6 (R5.2), S102.11, U123.12 (I5)
unnamed: S101.2, U121.4 (Q3a)
unnamed: S101.3, U121.5 (Q2a)
unnamed: S101.4, U121.6 (Q1a)
unnamed: S101.5, U121.7 (Q0a)
unnamed: S101.6, U121.12 (Q3b)
unnamed: S101.7, U121.11 (Q2b)
unnamed: S101.8, U121.10 (Q1b)
unnamed: S101.9, U121.9 (Q0b)
unnamed: U115.3, U123.1 (OEa)
unnamed: U115.11, U122.1 (OEa), U122.15 (OEb), U123.15 (OEb)
RST: RN112.3 (R2.2), U108.6
VCC: C129.2, C142.2, C143.1, C144.1, D124.1 (K), Q102.3 (C), R109.1 (common), R111.1 (common), RN112.1 (R1), U115.4, U115.5, U115.14 (VCC), U121.16 (VCC), U122.16 (VCC), U123.16 (VCC)
~A0XXX: U115.12, U121.2 (Ea2), U121.14 (Eb1)
~A1XXX: U115.1
~RD1: S101.12, U115.2, U115.13
~ROMGATE: S101.10
~VMEMBRDG: S101.11

Notes on the sheet:
THE KEYBOARD HOW QUAINT!
