misterblack1/zenith_zt1/ZT1 Schematics/modem.kicad_sch

## KiCad design ZT1 Schematics/modem.kicad_sch (2025-08-11)

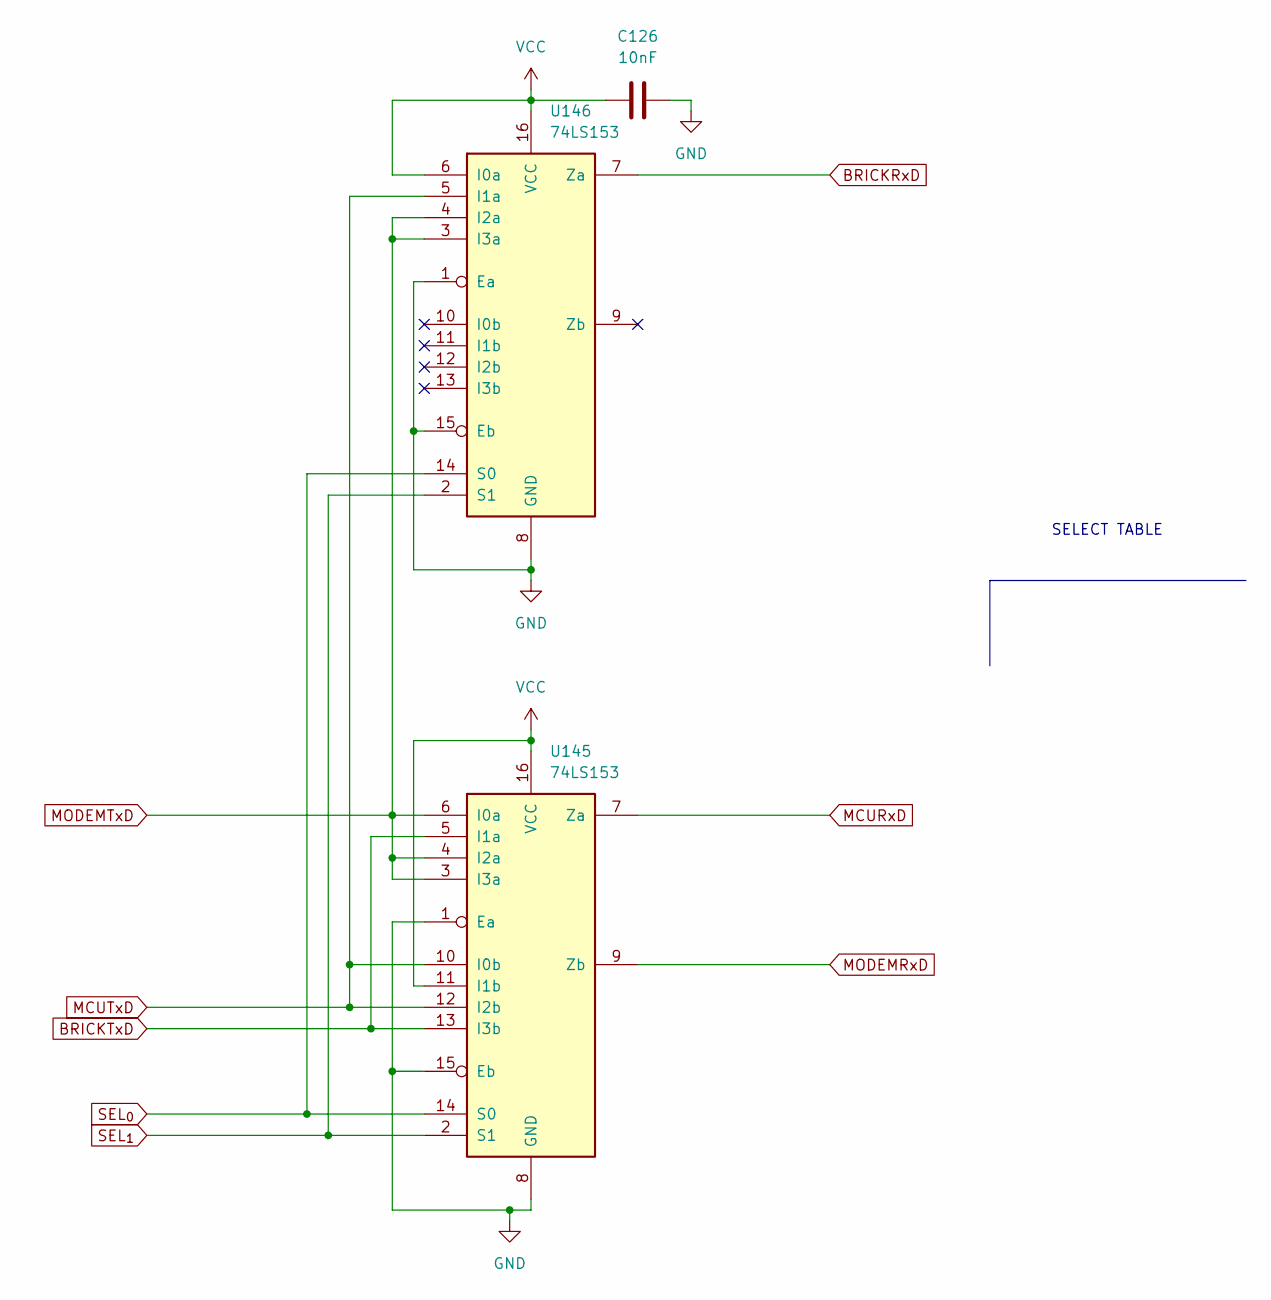
[picture p33: schematic modem.kicad_sch]

Parts:
C126: 10nF; C_350mil
U145, U146: 74LS153; DIP-16_W7.62mm

Connections:
BRICKRxD: U146.7 (Za)
BRICKTxD: U145.5 (I1a), U145.13 (I3b)
GND: C126.2, U145.1 (Ea), U145.8 (GND), U145.15 (Eb), U146.1 (Ea), U146.8 (GND), U146.15 (Eb)
MCURxD: U145.7 (Za)
MCUTxD: U145.10 (I0b), U145.12 (I2b), U146.5 (I1a)
MODEMRxD: U145.9 (Zb)
MODEMTxD: U145.3 (I3a), U145.4 (I2a), U145.6 (I0a), U146.3 (I3a), U146.4 (I2a)
SEL_{0}: U145.14 (S0), U146.14 (S0)
SEL_{1}: U145.2 (S1), U146.2 (S1)
VCC: C126.1, U145.11 (I1b), U145.16 (VCC), U146.6 (I0a), U146.16 (VCC)

Notes on the sheet:
SELECT TABLE
