misterblack1/zenith_zt1/ZT1 Schematics/printer.kicad_sch

## KiCad design ZT1 Schematics/printer.kicad_sch (2025-08-11)

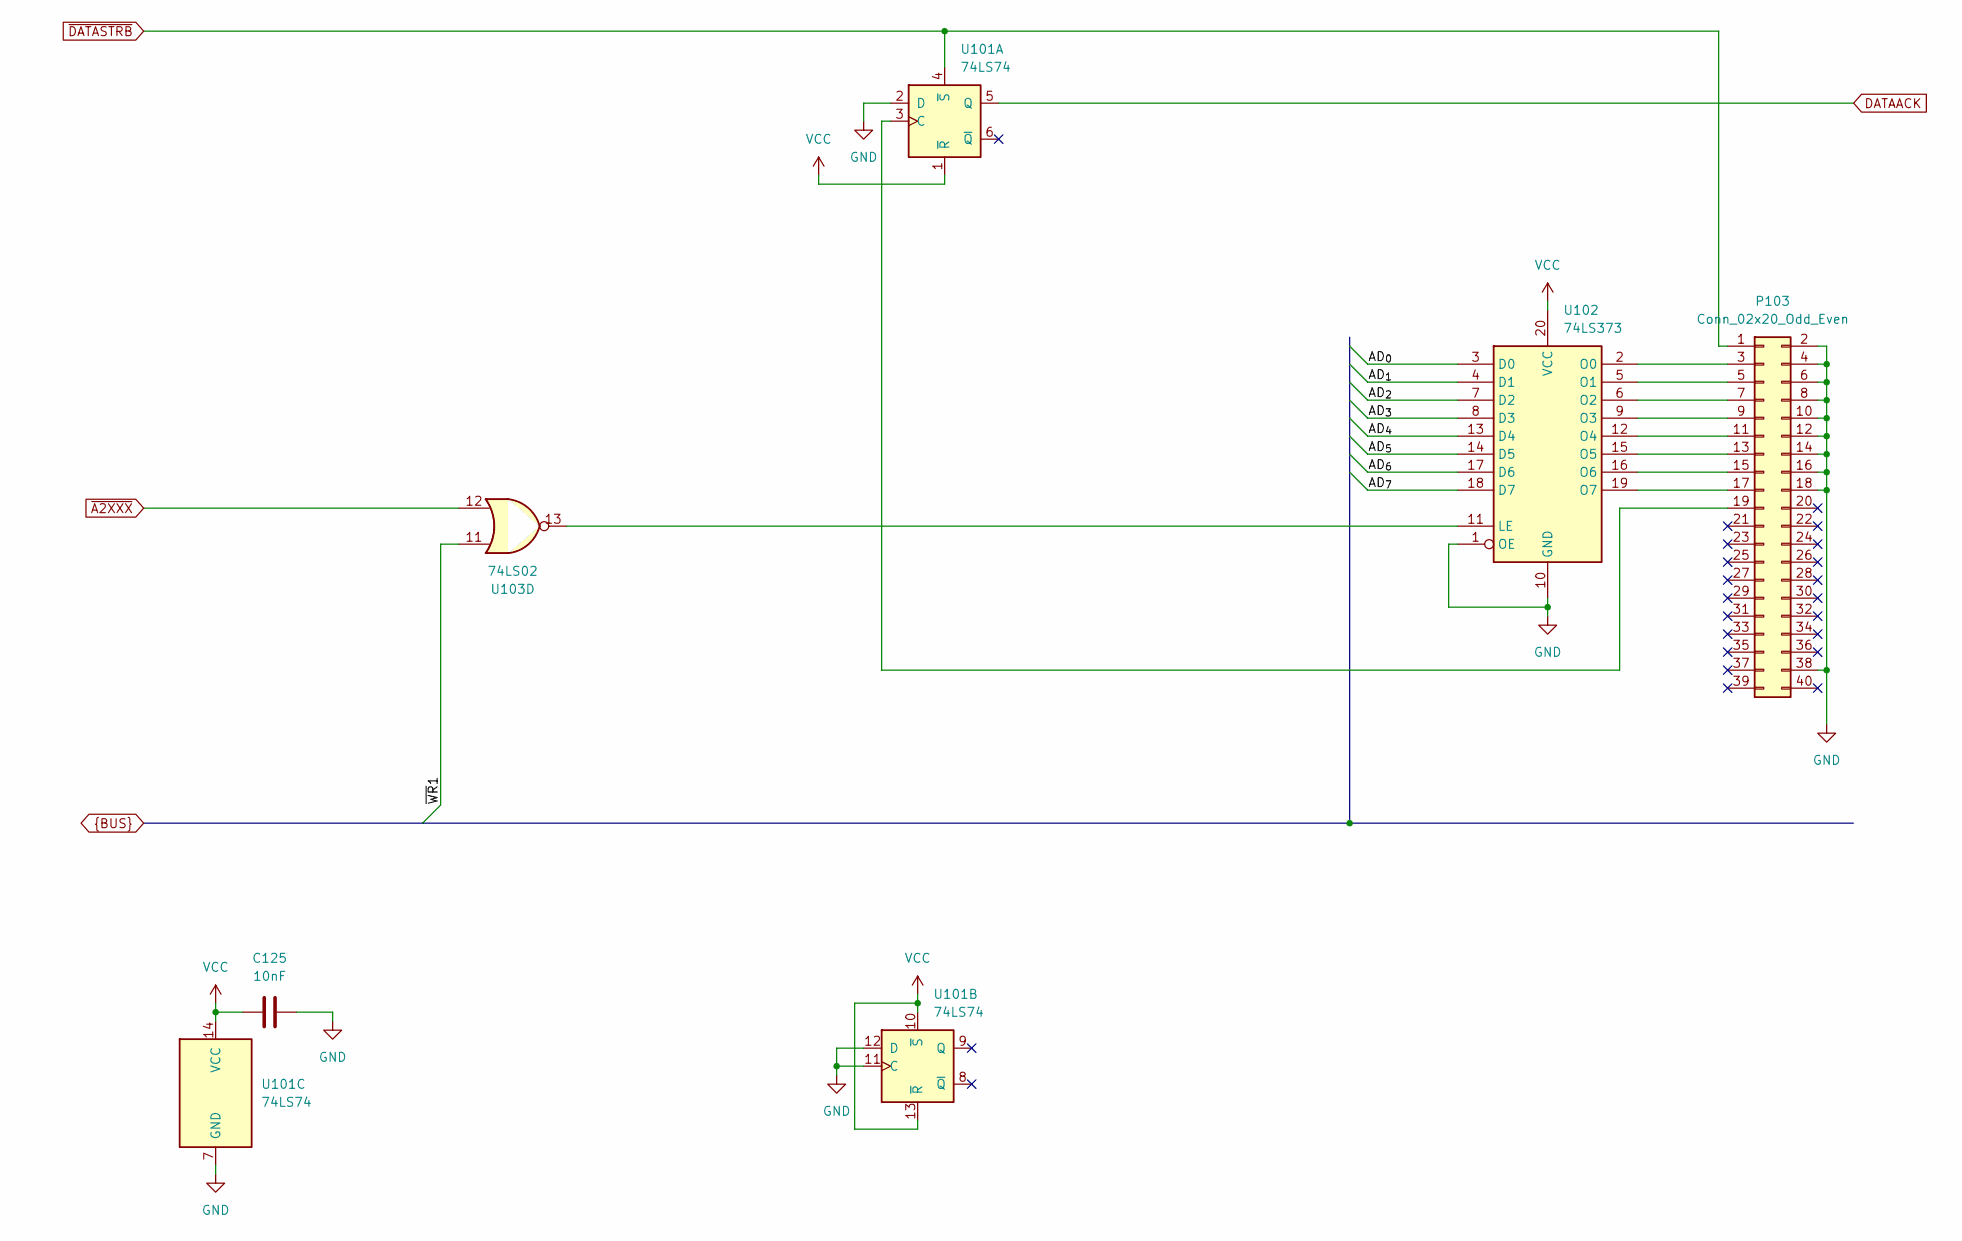
[picture p34: schematic printer.kicad_sch]

Parts:
C125: 10nF; C_350mil
P103: Conn_02x20_Odd_Even; PinHeader_2x20_P2.54mm_Horizontal
U101: 74LS74; DIP-14_W7.62mm
U102: 74LS373; DIP-20_W7.62mm
U103: 74LS02; DIP-14_W7.62mm

Connections:
AD_{0}: U102.3 (D0)
AD_{1}: U102.4 (D1)
AD_{2}: U102.7 (D2)
AD_{3}: U102.8 (D3)
AD_{4}: U102.13 (D4)
AD_{5}: U102.14 (D5)
AD_{6}: U102.17 (D6)
AD_{7}: U102.18 (D7)
DATAACK: U101.5 (Q)
GND: C125.2, P103.2, P103.4, P103.6, P103.8, P103.10, P103.12, P103.14, P103.16, P103.18, P103.38, U101.2 (D), U101.7 (GND), U101.11 (C), U101.12 (D), U102.1 (OE), U102.10 (GND)
unnamed: P103.3, U102.2 (O0)
unnamed: P103.5, U102.5 (O1)
unnamed: P103.7, U102.6 (O2)
unnamed: P103.9, U102.9 (O3)
unnamed: P103.11, U102.12 (O4)
unnamed: P103.13, U102.15 (O5)
unnamed: P103.15, U102.16 (O6)
unnamed: P103.17, U102.19 (O7)
unnamed: P103.19, U101.3 (C)
unnamed: U102.11 (LE), U103.13
VCC: C125.1, U101.1 (~R), U101.10 (~S), U101.13 (~R), U101.14 (VCC), U102.20 (VCC)
~A2XXX: U103.12
~DATASTRB: P103.1, U101.4 (~S)
~WR1: U103.11
