misterblack1/zenith_zt1/ZT1 Schematics/video.kicad_sch

## KiCad design ZT1 Schematics/video.kicad_sch (2025-08-11)

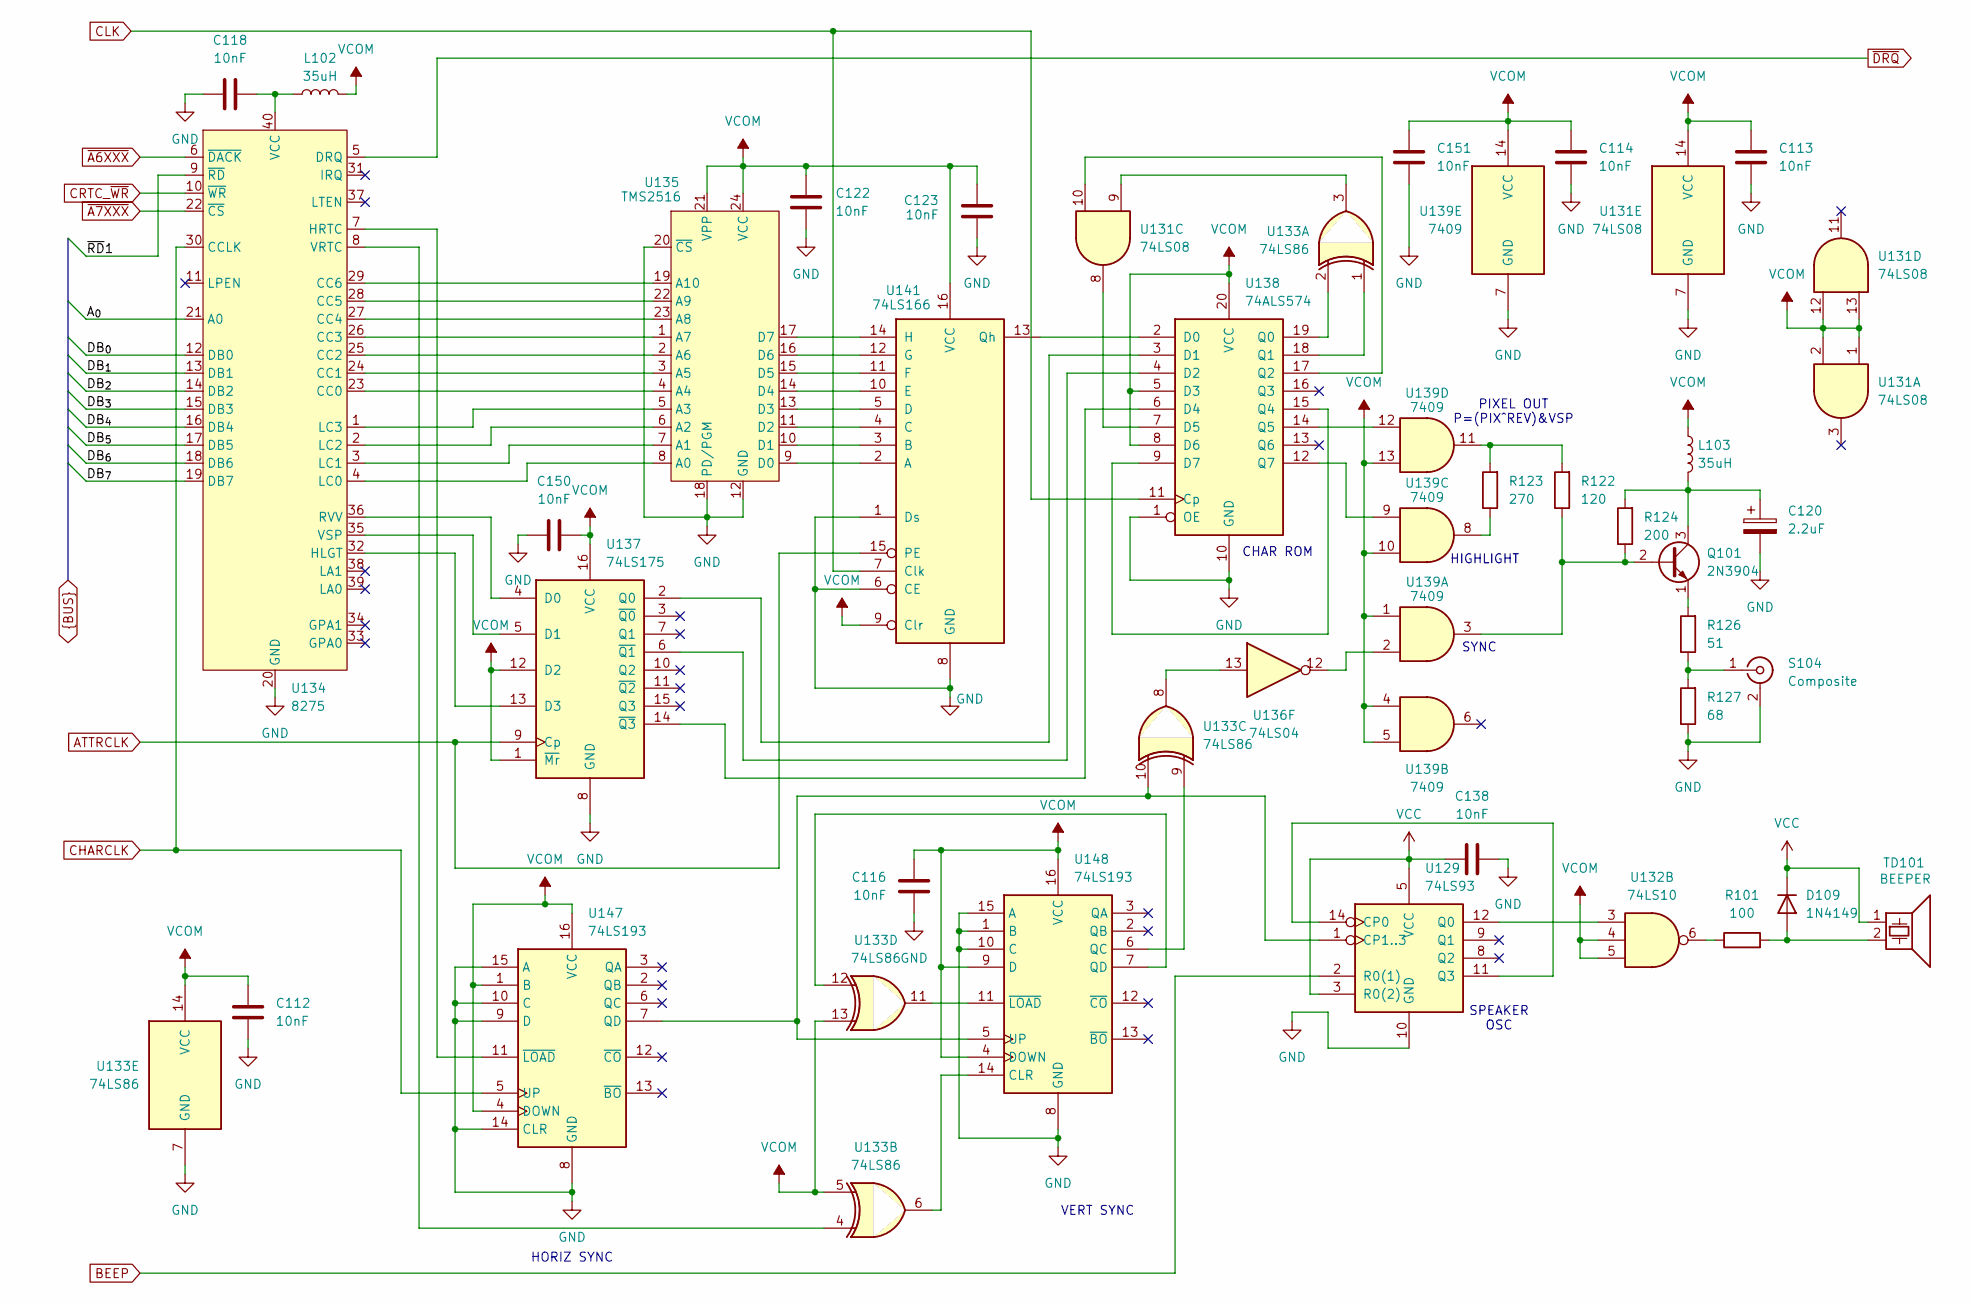
[picture p35: schematic video.kicad_sch]

Parts:
C112, C113, C114, C116, C118, C122, C123, C138, C150, C151: 10nF; C_350mil
C120: 2.2uF; CP_520mil
D109: 1N4149; D_350mil
L102, L103: 35uH; L_Axial_L7.0mm_D3.3mm_P5.08mm_Vertical_Fastron_MICC
Q101: 2N3904; TO-92L_Inline_Wide
R101: 100; R_450mil
R122: 120; R_450mil
R123: 270; R_450mil
R124: 200; R_450mil
R126: 51; R_450mil
R127: 68; R_450mil
S104: Composite; RCA
TD101: BEEPER; Buzzer_12x9.5RM7.6
U129: 74LS93; DIP-14_W7.62mm
U131: 74LS08; DIP-14_W7.62mm
U132: 74LS10; DIP-14_W7.62mm
U133: 74LS86; DIP-14_W7.62mm
U134: 8275; DIP-40_W15.24mm_Socket
U135: TMS2516; DIP-24_W15.24mm
U136: 74LS04; DIP-14_W7.62mm
U137: 74LS175; DIP-16_W7.62mm
U138: 74ALS574; DIP-20_W7.62mm
U139: 7409; DIP-14_W7.62mm
U141: 74LS166; DIP-16_W7.62mm
U147, U148: 74LS193; DIP-16_W7.62mm

Connections:
ATTRCLK: U137.9 (Cp), U141.15 (PE)
A_{0}: U134.21 (A0)
BEEP: U129.2 (R0(1))
CHARCLK: U134.30 (CCLK), U147.5 (UP)
CLK: U138.11 (Cp), U141.7 (Clk)
CRTC_~WR: U134.10 (~WR)
DB_{0}: U134.12 (DB0)
DB_{1}: U134.13 (DB1)
DB_{2}: U134.14 (DB2)
DB_{3}: U134.15 (DB3)
DB_{4}: U134.16 (DB4)
DB_{5}: U134.17 (DB5)
DB_{6}: U134.18 (DB6)
DB_{7}: U134.19 (DB7)
GND: C112.2, C113.2, C114.2, C116.2, C118.1, C120.2, C122.2, C123.2, C138.2, C150.1, C151.2, R127.1, S104.2 (Ext), U129.10 (GND), U131.7 (GND), U133.7 (GND), U134.20 (GND), U135.12 (GND), U135.18 (PD/PGM), U135.20 (~CS), U137.8 (GND), U138.1 (OE), U138.10 (GND), U139.7 (GND), U141.1 (Ds), U141.6 (CE), U141.8 (GND), U147.8 (GND), U147.9 (D), U147.10 (C), U147.14 (CLR), U147.15 (A), U148.1 (B), U148.8 (GND), U148.10 (C), U148.15 (A)
unnamed: C118.2, L102.1, U134.40 (VCC)
unnamed: C120.1, L103.2, Q101.3 (C), R124.2
unnamed: D109.2 (A), R101.2, TD101.2
unnamed: Q101.1 (E), R126.2
unnamed: Q101.2 (B), R122.1, R124.1, U139.3
unnamed: R101.1, U132.6
unnamed: R122.2, R123.2, U139.11
unnamed: R123.1, U139.8
unnamed: R126.1, R127.2, S104.1 (In)
unnamed: U129.1 (CP1..3), U133.10, U147.7 (QD), U148.5 (UP)
unnamed: U129.11 (Q3), U129.14 (CP0)
unnamed: U129.12 (Q0), U132.3
unnamed: U131.8, U138.7 (D5)
unnamed: U131.9, U133.3
unnamed: U131.10, U138.17 (Q2)
unnamed: U133.1, U138.18 (Q1)
unnamed: U133.2, U138.19 (Q0)
unnamed: U133.4, U134.8 (VRTC)
unnamed: U133.6, U148.14 (CLR)
unnamed: U133.8, U136.13
unnamed: U133.9, U148.6 (QC)
unnamed: U133.11, U148.11 (~LOAD)
unnamed: U133.12, U148.7 (QD)
unnamed: U134.1 (LC3), U135.5 (A3)
unnamed: U134.2 (LC2), U135.6 (A2)
unnamed: U134.3 (LC1), U135.7 (A1)
unnamed: U134.4 (LC0), U135.8 (A0)
unnamed: U134.7 (HRTC), U147.11 (~LOAD)
unnamed: U134.23 (CC0), U135.4 (A4)
unnamed: U134.24 (CC1), U135.3 (A5)
unnamed: U134.25 (CC2), U135.2 (A6)
unnamed: U134.26 (CC3), U135.1 (A7)
unnamed: U134.27 (CC4), U135.23 (A8)
unnamed: U134.28 (CC5), U135.22 (A9)
unnamed: U134.29 (CC6), U135.19 (A10)
unnamed: U134.32 (HLGT), U137.13 (D3)
unnamed: U134.35 (VSP), U137.5 (D1)
unnamed: U134.36 (RVV), U137.4 (D0)
unnamed: U135.9 (D0), U141.2 (A)
unnamed: U135.10 (D1), U141.3 (B)
unnamed: U135.11 (D2), U141.4 (C)
unnamed: U135.13 (D3), U141.5 (D)
unnamed: U135.14 (D4), U141.10 (E)
unnamed: U135.15 (D5), U141.11 (F)
unnamed: U135.16 (D6), U141.12 (G)
unnamed: U135.17 (D7), U141.14 (H)
unnamed: U136.12, U139.2
unnamed: U137.2 (Q0), U138.3 (D1)
unnamed: U137.6 (~Q1), U138.4 (D2)
unnamed: U137.14 (~Q3), U138.6 (D4)
unnamed: U138.2 (D0), U141.13 (Qh)
unnamed: U138.12 (Q7), U139.9
unnamed: U138.14 (Q5), U139.12
unnamed: U138.9 (D7), U138.15 (Q4)
VCC: C138.1, D109.1 (K), TD101.1, U129.3 (R0(2)), U129.5 (VCC)
VCOM: C112.1, C113.1, C114.1, C116.1, C122.1, C123.1, C150.2, C151.1, L102.2, L103.1, U131.1, U131.2, U131.12, U131.13, U131.14 (VCC), U132.4, U132.5, U133.5, U133.13, U133.14 (VCC), U135.21 (VPP), U135.24 (VCC), U137.1 (~Mr), U137.12 (D2), U137.16 (VCC), U138.5 (D3), U138.8 (D6), U138.20 (VCC), U139.1, U139.4, U139.5, U139.10, U139.13, U139.14 (VCC), U141.9 (Clr), U141.16 (VCC), U147.1 (B), U147.4 (DOWN), U147.16 (VCC), U148.4 (DOWN), U148.9 (D), U148.16 (VCC)
~A6XXX: U134.6 (~DACK)
~A7XXX: U134.22 (~CS)
~DRQ: U134.5 (DRQ)
~RD1: U134.9 (~RD)

Notes on the sheet:
VERT SYNC
HIGHLIGHT
SPEAKER OSC
PIXEL OUT P=(PIX^REV)&VSP
SYNC
HORIZ SYNC
CHAR ROM
